yanagi-kimuralab/opensource-platform/OpenSource-Platform for publication/Parts/Driving crawler_Tensioner_Positioning plate _Inside.SLDPRT

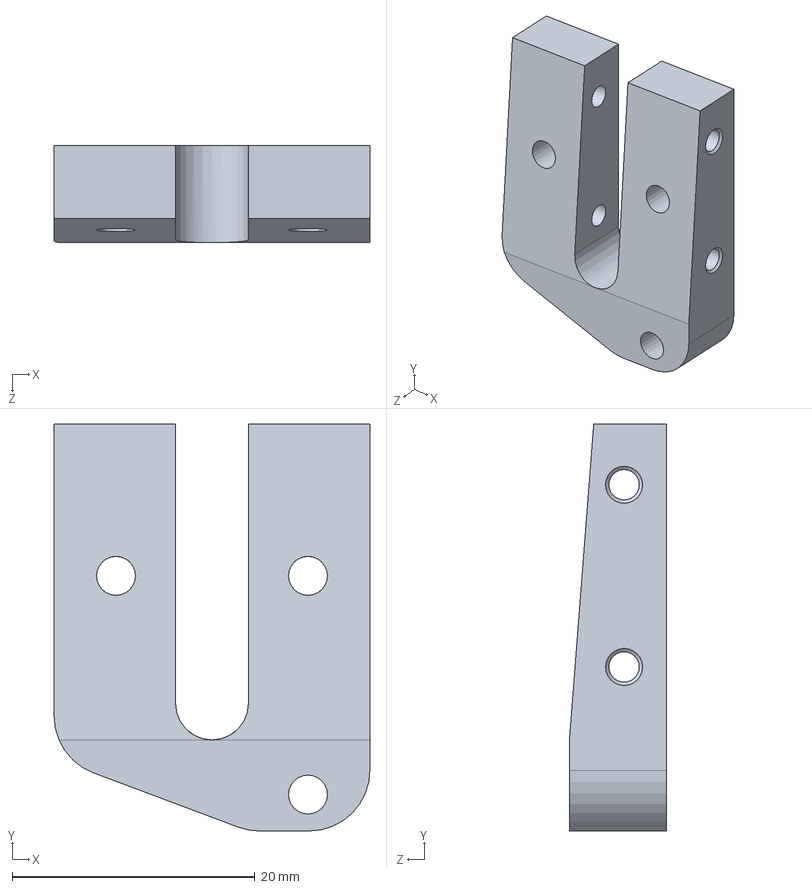
[picture p15: CAD file, 2023-01-07, last stored version]
OpenSource-Platform for publication/Parts/Driving crawler_Tensioner_Positioning plate _Inside.SLDPRT
26.0 x 33.5 x 8.00 mm
