yanagi-kimuralab/opensource-platform/OpenSource-Platform for publication/Ready-madeParts/PIJJ14-8-87.SLDPRT

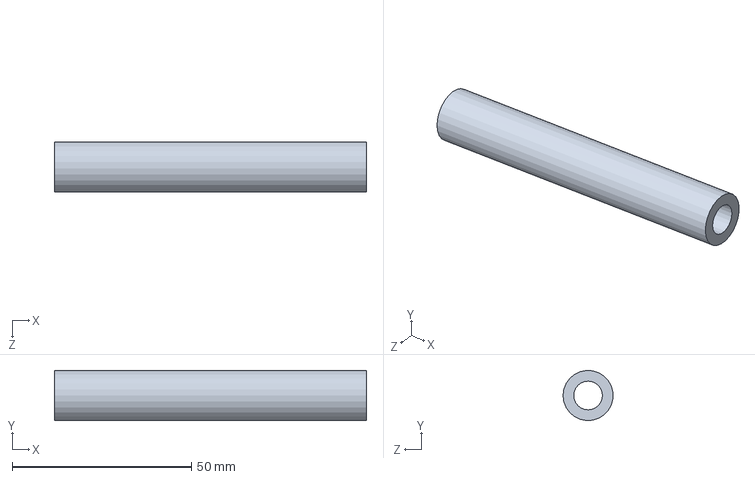
[picture p16: CAD file, 2023-01-07, last stored version]
OpenSource-Platform for publication/Ready-madeParts/PIJJ14-8-87.SLDPRT
87.0 x 14.0 x 13.9 mm
