yanagi-kimuralab/opensource-platform/OpenSource-Platform for publication/Ready-madeParts/内臓/NUC11PAHi7.SLDPRT

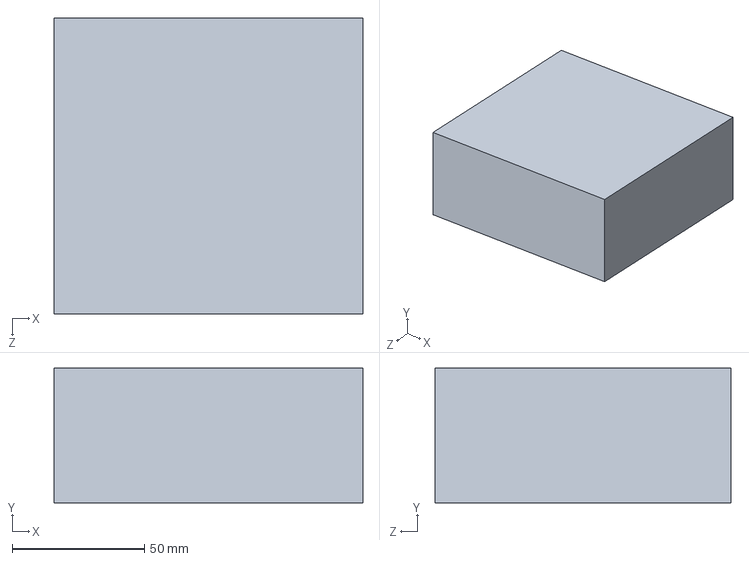
[picture p17: CAD file, 2023-01-07, last stored version]
OpenSource-Platform for publication/Ready-madeParts/内臓/NUC11PAHi7.SLDPRT
117.0 x 51.0 x 112.0 mm
