yanagi-kimuralab/opensource-platform/OpenSource-Platform for publication/jig/Flipper belt making jig.SLDPRT

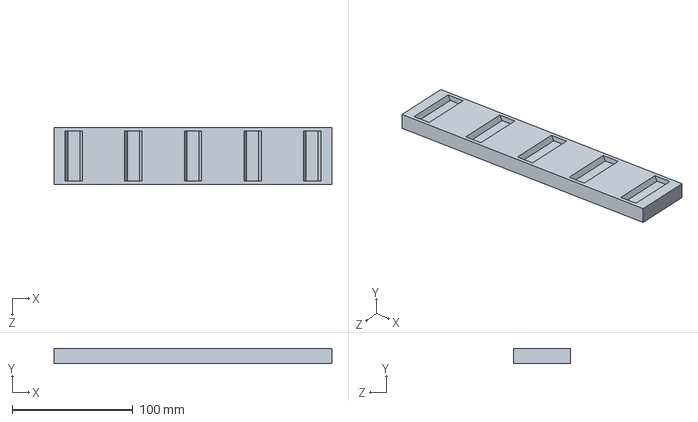
[picture p18: CAD file, 2023-01-07, last stored version]
OpenSource-Platform for publication/jig/Flipper belt making jig.SLDPRT
230.0 x 12.0 x 47.5 mm
