yanagi-kimuralab/opensource-platform/OpenSource-Platform for publication/Parts/Driving crawler_Tensioner_Shaft attachment.SLDPRT

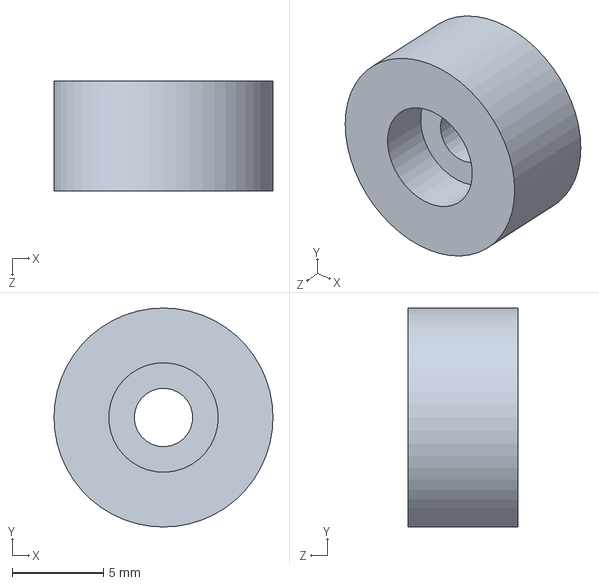
[picture p19: CAD file, 2023-01-07, last stored version]
OpenSource-Platform for publication/Parts/Driving crawler_Tensioner_Shaft attachment.SLDPRT
12.0 x 12.0 x 6.00 mm
