yanagi-kimuralab/opensource-platform/OpenSource-Platform for publication/Ready-madeParts/SLP9000A.SLDPRT

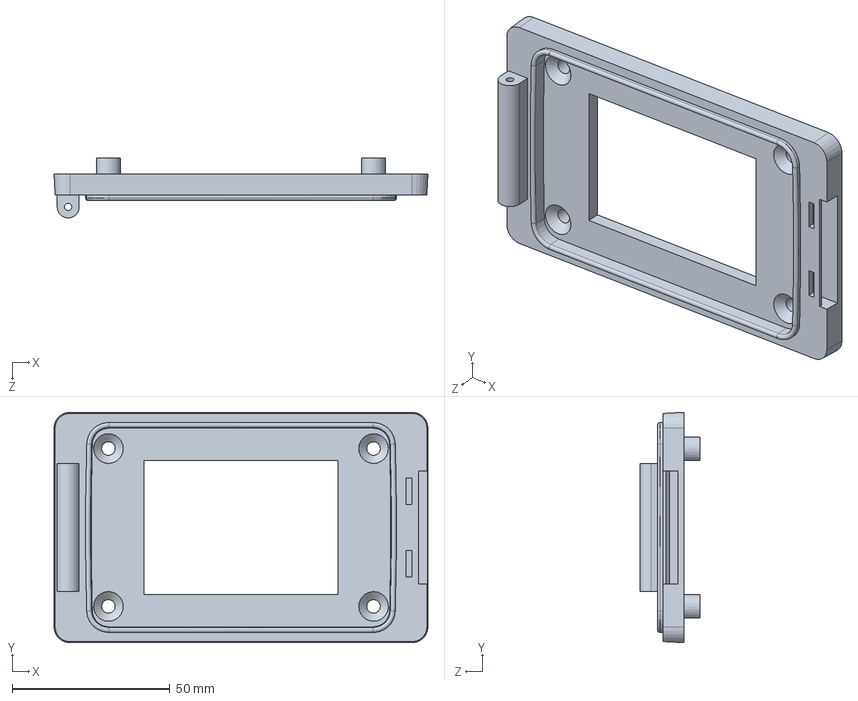
[picture p20: CAD file, 2023-01-07, last stored version]
OpenSource-Platform for publication/Ready-madeParts/SLP9000A.SLDPRT
118.5 x 73.0 x 19.0 mm
