yanagi-kimuralab/opensource-platform/OpenSource-Platform for publication/Ready-madeParts/内臓/ビデオサーバ.SLDPRT

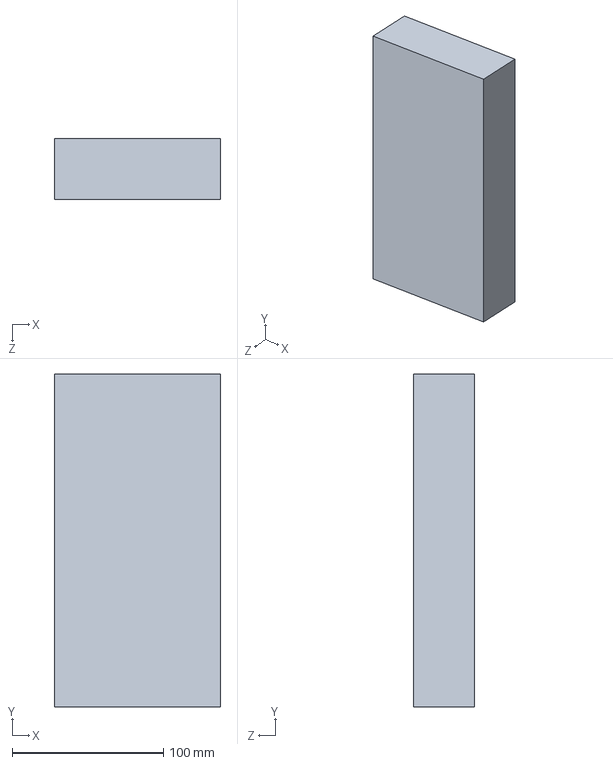
[picture p21: CAD file, 2023-01-07, last stored version]
OpenSource-Platform for publication/Ready-madeParts/内臓/ビデオサーバ.SLDPRT
110.0 x 220.0 x 40.0 mm
