yanagi-kimuralab/opensource-platform/OpenSource-Platform for publication/jig/Wart rubber cutting jig.SLDPRT

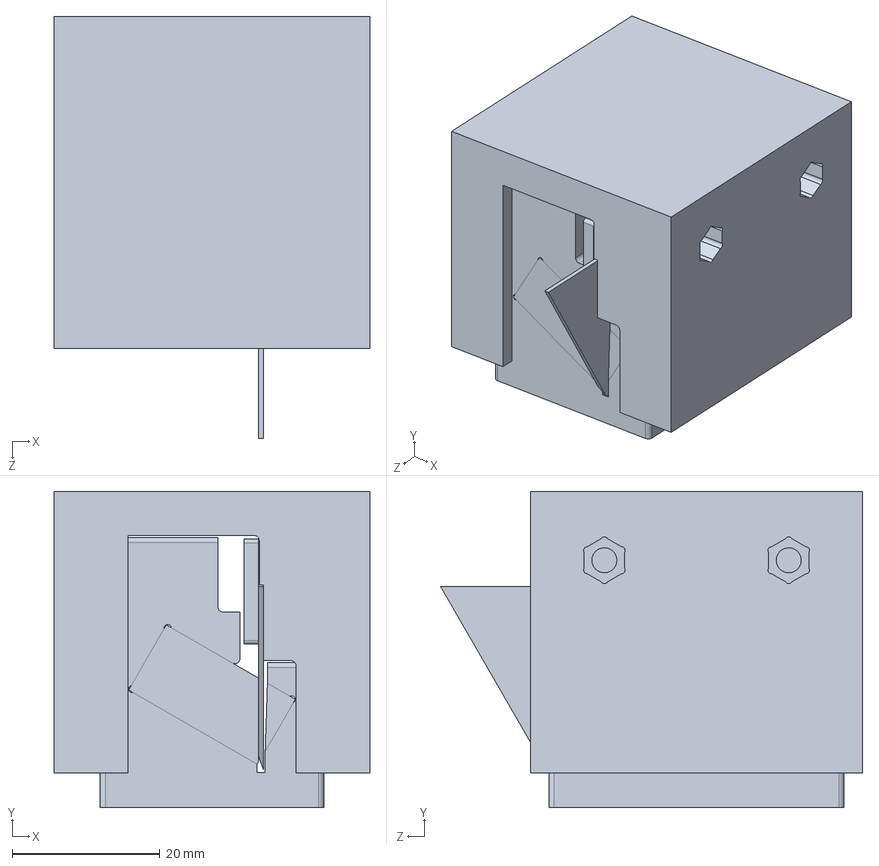
[picture p22: CAD file, 2023-01-07, last stored version]
OpenSource-Platform for publication/jig/Wart rubber cutting jig.SLDPRT
42.8 x 42.9 x 57.2 mm
