yanagi-kimuralab/opensource-platform/OpenSource-Platform for publication/Ready-madeParts/RDOS8-49.2-WMC4.SLDPRT

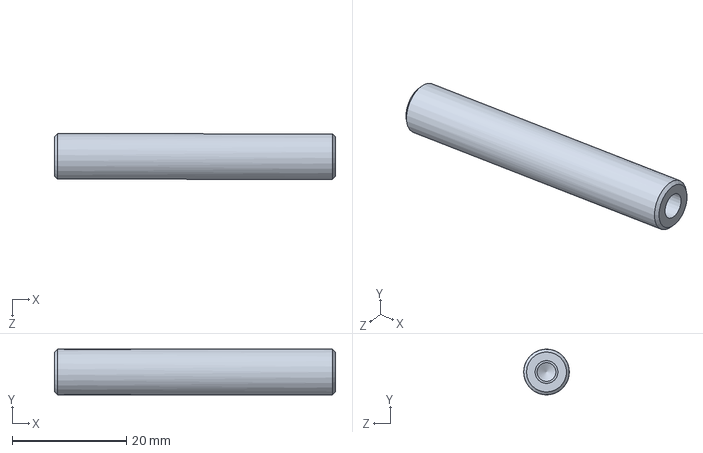
[picture p24: CAD file, 2023-01-07, last stored version]
OpenSource-Platform for publication/Ready-madeParts/RDOS8-49.2-WMC4.SLDPRT
49.2 x 7.98 x 8.00 mm
