yanagi-kimuralab/opensource-platform/OpenSource-Platform for publication/Ready-madeParts/内臓/バッテリー.SLDPRT

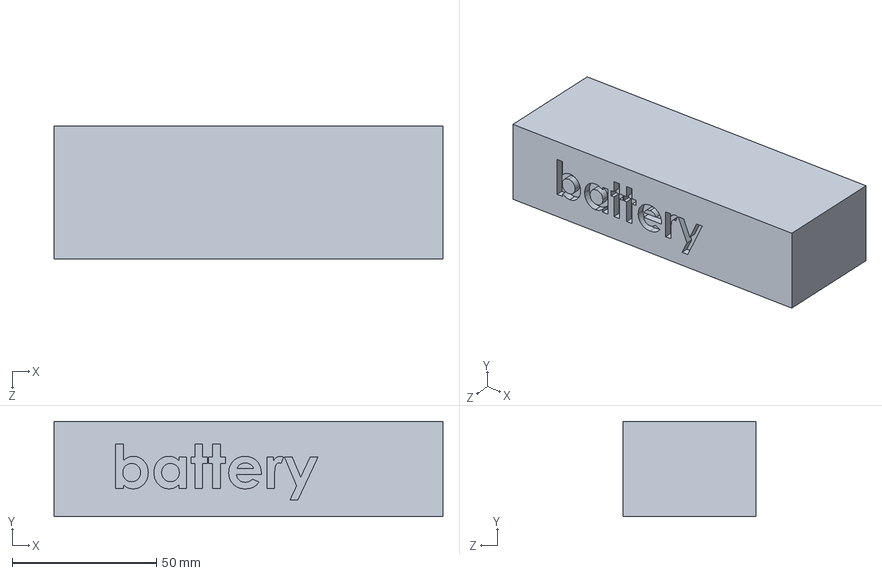
[picture p25: CAD file, 2023-01-07, last stored version]
OpenSource-Platform for publication/Ready-madeParts/内臓/バッテリー.SLDPRT
135.0 x 33.0 x 46.0 mm
