yanagi-kimuralab/opensource-platform/OpenSource-Platform for publication/Parts/Driving crawler_Tensioner_Positioning plate _Outside.SLDPRT

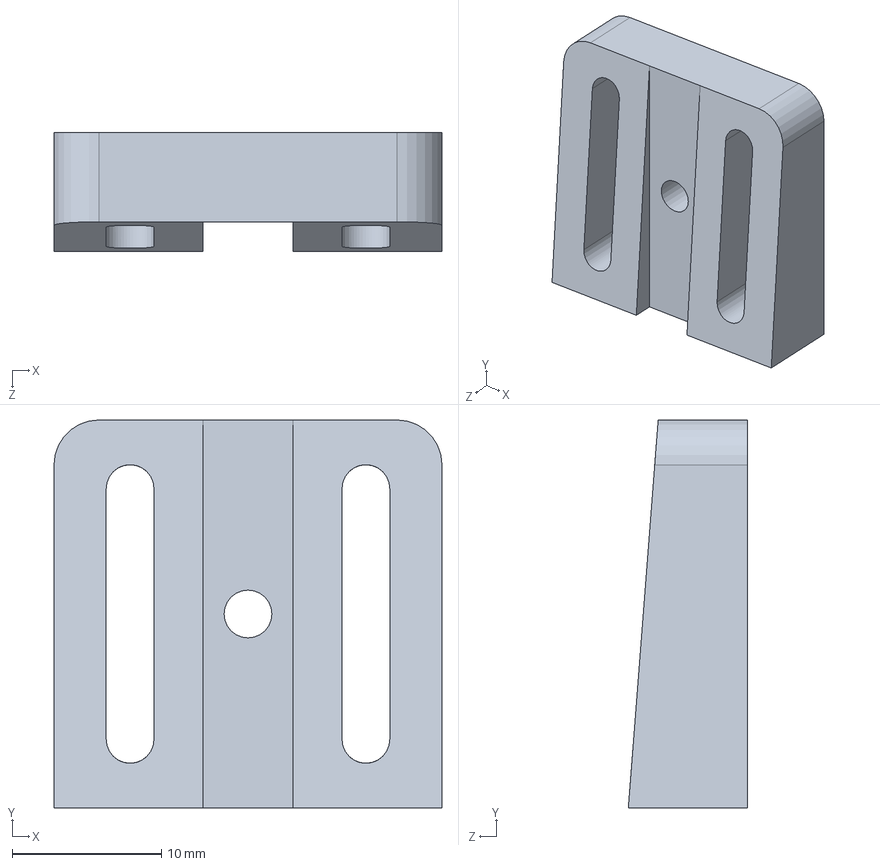
[picture p26: CAD file, 2023-01-07, last stored version]
OpenSource-Platform for publication/Parts/Driving crawler_Tensioner_Positioning plate _Outside.SLDPRT
26.0 x 26.0 x 8.00 mm
