yanagi-kimuralab/opensource-platform/OpenSource-Platform for publication/Ready-madeParts/SLP9000C.SLDPRT

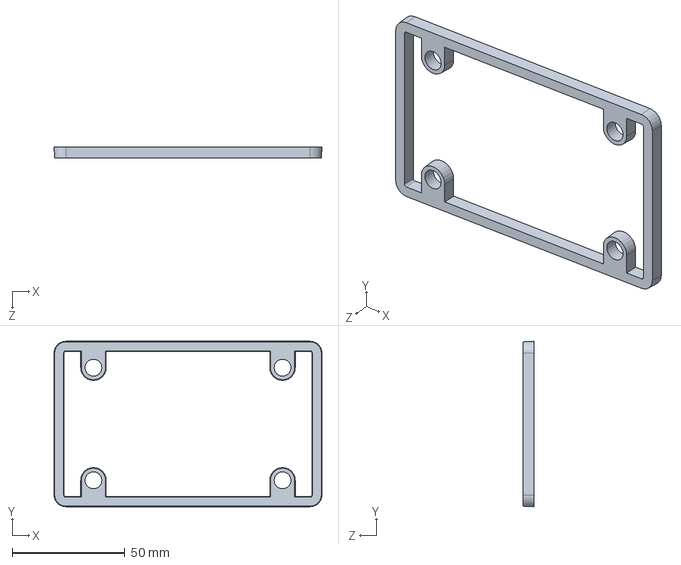
[picture p27: CAD file, 2023-01-07, last stored version]
OpenSource-Platform for publication/Ready-madeParts/SLP9000C.SLDPRT
119.0 x 73.5 x 5.00 mm
