yanagi-kimuralab/opensource-platform/OpenSource-Platform for publication/Parts/Driving crawler_Holding timing pulley plate_Base.SLDPRT

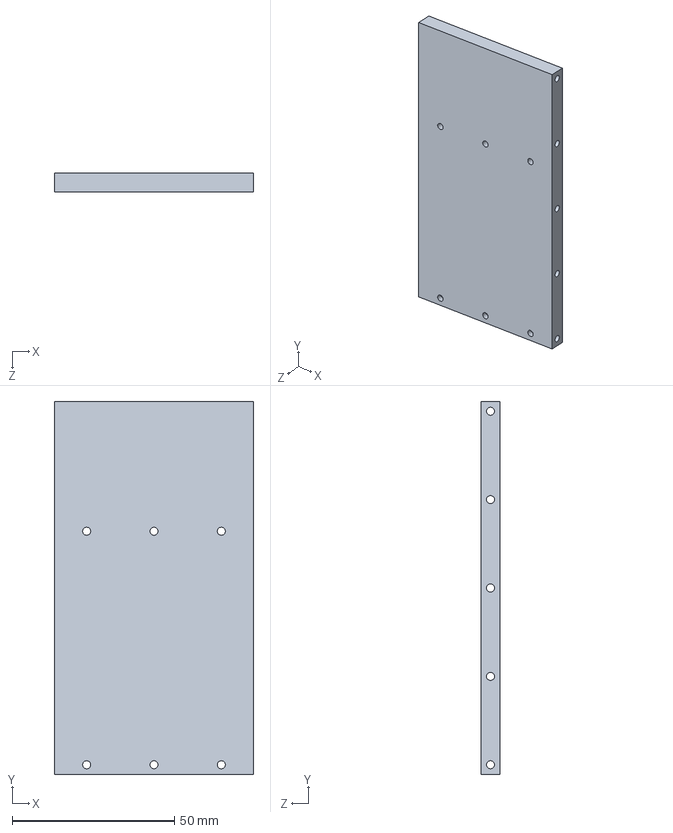
[picture p28: CAD file, 2023-01-07, last stored version]
OpenSource-Platform for publication/Parts/Driving crawler_Holding timing pulley plate_Base.SLDPRT
61.5 x 115.0 x 6.00 mm
