yanagi-kimuralab/opensource-platform/OpenSource-Platform for publication/Ready-madeParts/RDOS8-95-WMC4.SLDPRT

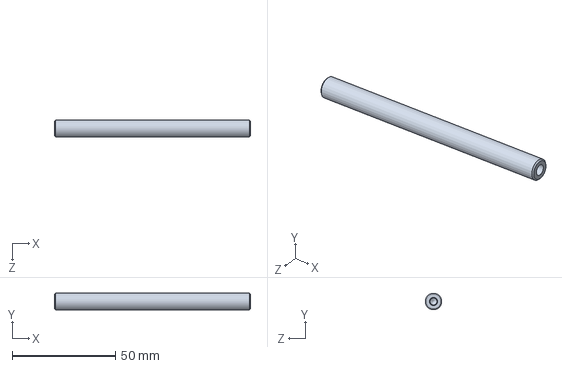
[picture p29: CAD file, 2023-01-07, last stored version]
OpenSource-Platform for publication/Ready-madeParts/RDOS8-95-WMC4.SLDPRT
95.0 x 8.00 x 8.00 mm
