yanagi-kimuralab/opensource-platform/OpenSource-Platform for publication/Ready-madeParts/内臓/OPENCR.SLDPRT

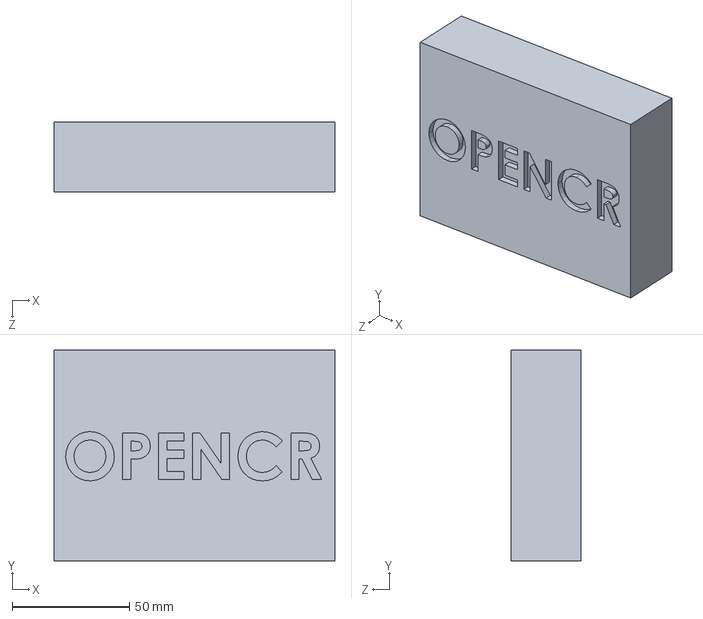
[picture p30: CAD file, 2023-01-07, last stored version]
OpenSource-Platform for publication/Ready-madeParts/内臓/OPENCR.SLDPRT
120.0 x 90.0 x 30.0 mm
