yanagi-kimuralab/opensource-platform/OpenSource-Platform for publication/Lid.sldprt

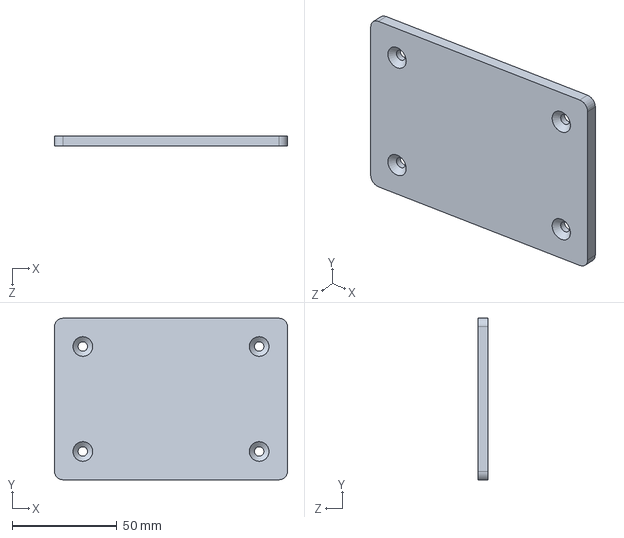
[picture p31: CAD file, 2023-01-07, last stored version]
OpenSource-Platform for publication/Lid.sldprt
111.0 x 77.0 x 5.00 mm
