yanagi-kimuralab/opensource-platform/OpenSource-Platform for publication/Parts/Driving crawler_Motor box_Plate_Side L R.SLDPRT

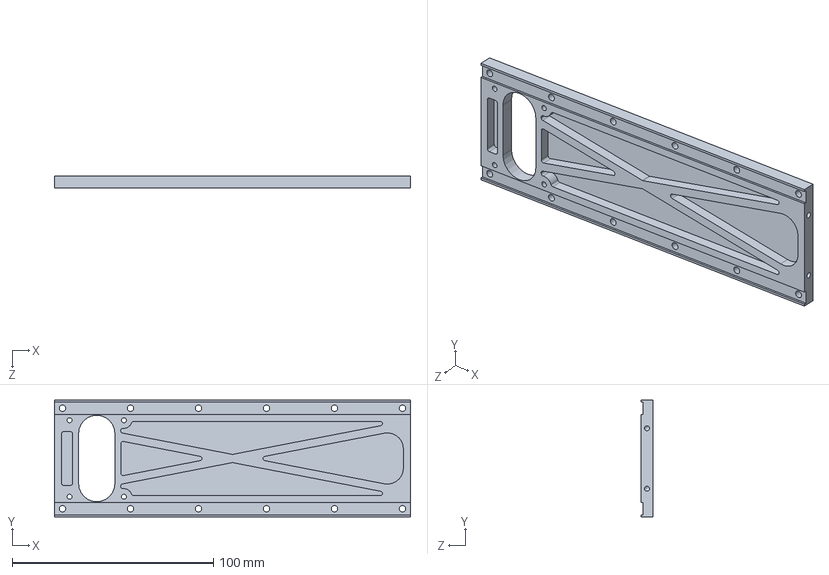
[picture p32: CAD file, 2023-01-07, last stored version]
OpenSource-Platform for publication/Parts/Driving crawler_Motor box_Plate_Side L R.SLDPRT
177.0 x 58.0 x 6.00 mm
