yanagi-kimuralab/opensource-platform/OpenSource-Platform for publication/Ready-madeParts/H54-200-S500-R.SLDPRT

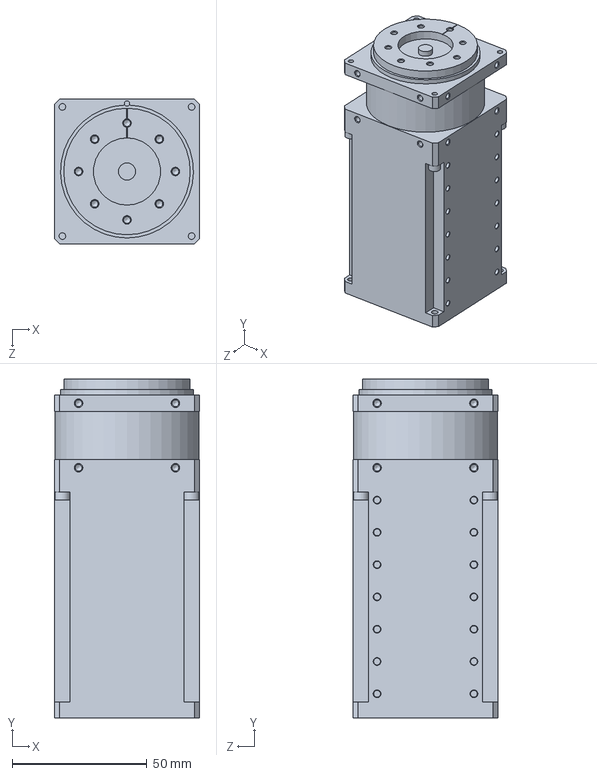
[picture p33: CAD file, 2023-01-07, last stored version]
OpenSource-Platform for publication/Ready-madeParts/H54-200-S500-R.SLDPRT
54.0 x 126.0 x 54.0 mm
