yanagi-kimuralab/opensource-platform/OpenSource-Platform for publication/Ready-madeParts/内臓/KYPOM K6 22.2V 3700mA 35C-70C.SLDPRT

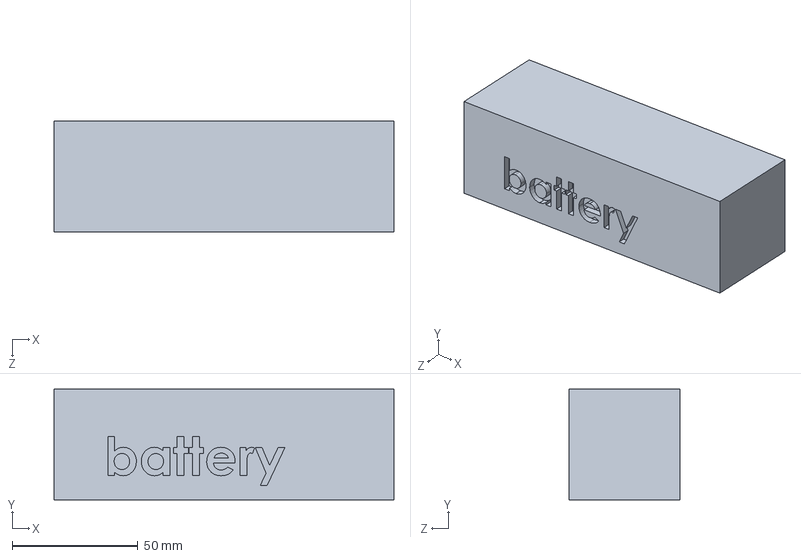
[picture p34: CAD file, 2023-01-07, last stored version]
OpenSource-Platform for publication/Ready-madeParts/内臓/KYPOM K6 22.2V 3700mA 35C-70C.SLDPRT
135.0 x 44.0 x 44.0 mm
