yanagi-kimuralab/opensource-platform/OpenSource-Platform for publication/Parts/Flipper_Connecting claw.SLDPRT

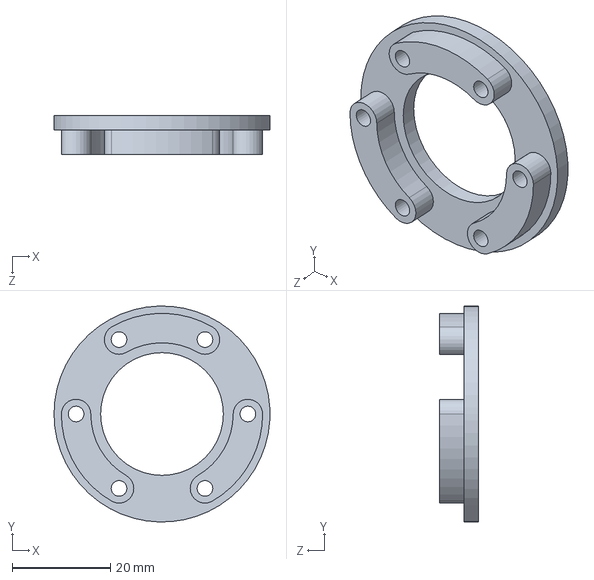
[picture p35: CAD file, 2023-01-07, last stored version]
OpenSource-Platform for publication/Parts/Flipper_Connecting claw.SLDPRT
44.0 x 44.0 x 8.00 mm
