yanagi-kimuralab/opensource-platform/OpenSource-Platform for publication/Ready-madeParts/FL6805ZZ.SLDPRT

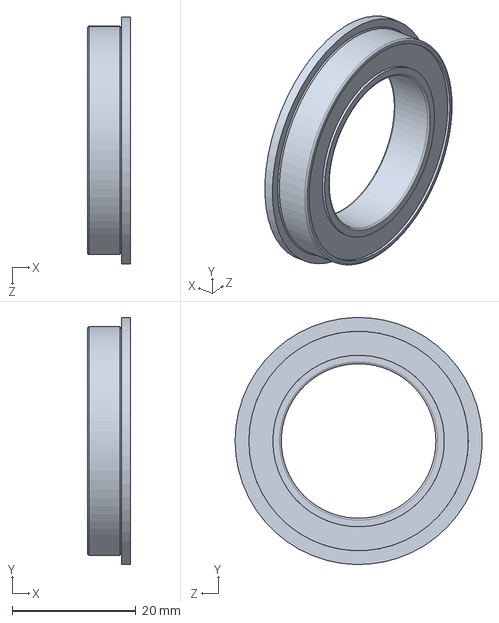
[picture p36: CAD file, 2023-01-07, last stored version]
OpenSource-Platform for publication/Ready-madeParts/FL6805ZZ.SLDPRT
7.00 x 40.0 x 40.0 mm
