yanagi-kimuralab/opensource-platform/OpenSource-Platform for publication/Ready-madeParts/内臓/48to24.SLDPRT

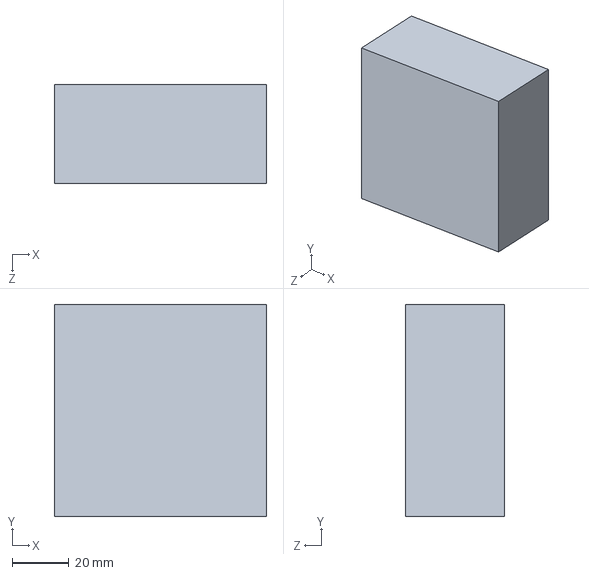
[picture p37: CAD file, 2023-01-07, last stored version]
OpenSource-Platform for publication/Ready-madeParts/内臓/48to24.SLDPRT
75.0 x 75.0 x 35.0 mm
