yanagi-kimuralab/opensource-platform/OpenSource-Platform for publication/Parts/Flipper_Timing pulley_Partition plate.SLDPRT

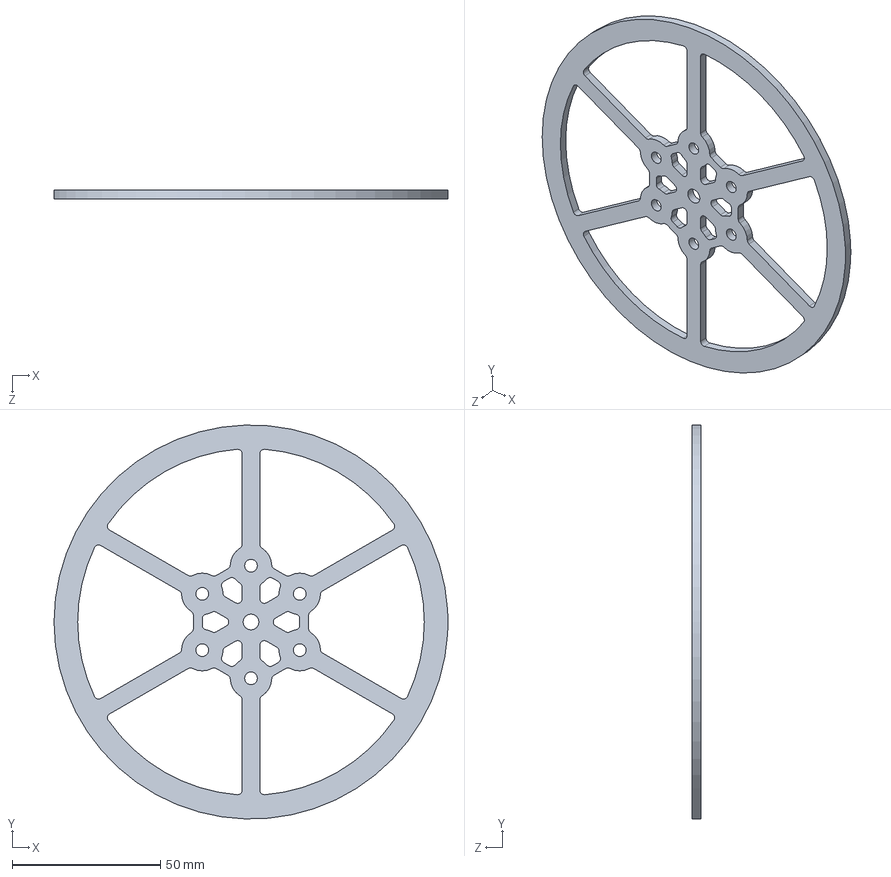
[picture p38: CAD file, 2023-01-07, last stored version]
OpenSource-Platform for publication/Parts/Flipper_Timing pulley_Partition plate.SLDPRT
133.0 x 132.9 x 3.00 mm
