yanagi-kimuralab/opensource-platform/OpenSource-Platform for publication/Ready-madeParts/KESF5-LC23.SLDPRT

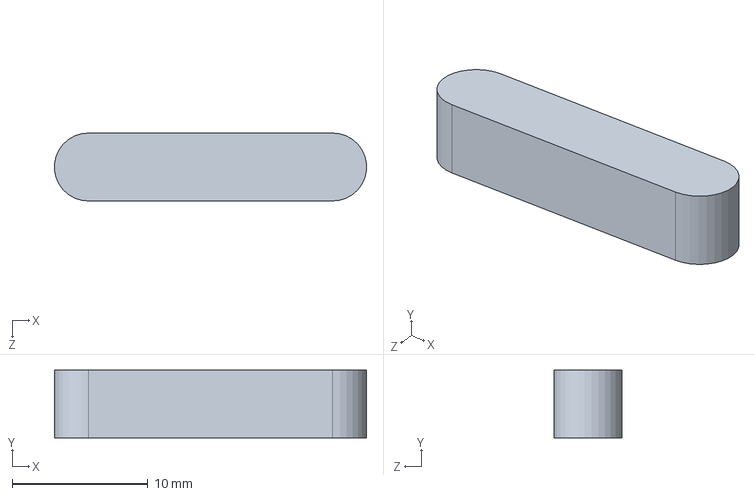
[picture p39: CAD file, 2023-01-07, last stored version]
OpenSource-Platform for publication/Ready-madeParts/KESF5-LC23.SLDPRT
23.0 x 5.00 x 5.00 mm
