yanagi-kimuralab/opensource-platform/OpenSource-Platform for publication/Ready-madeParts/内臓/NUC.SLDPRT

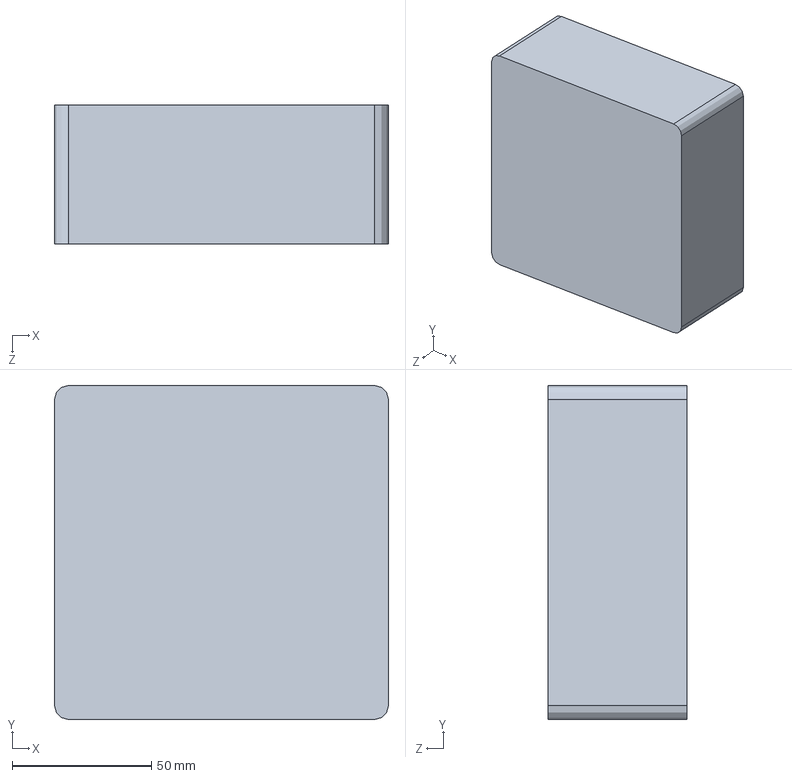
[picture p40: CAD file, 2023-01-07, last stored version]
OpenSource-Platform for publication/Ready-madeParts/内臓/NUC.SLDPRT
120.0 x 120.0 x 50.0 mm
