yanagi-kimuralab/opensource-platform/OpenSource-Platform for publication/Parts/Flipper_Timing pulley_Center attachment.SLDPRT

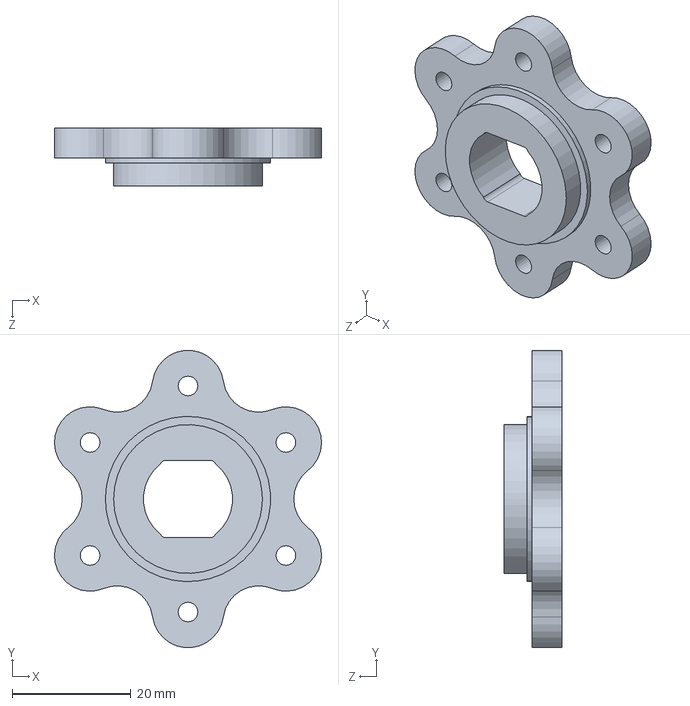
[picture p41: CAD file, 2023-01-07, last stored version]
OpenSource-Platform for publication/Parts/Flipper_Timing pulley_Center attachment.SLDPRT
44.9 x 49.9 x 9.70 mm
