yanagi-kimuralab/opensource-platform/OpenSource-Platform for publication/Ready-madeParts/B6800ZZ.SLDPRT

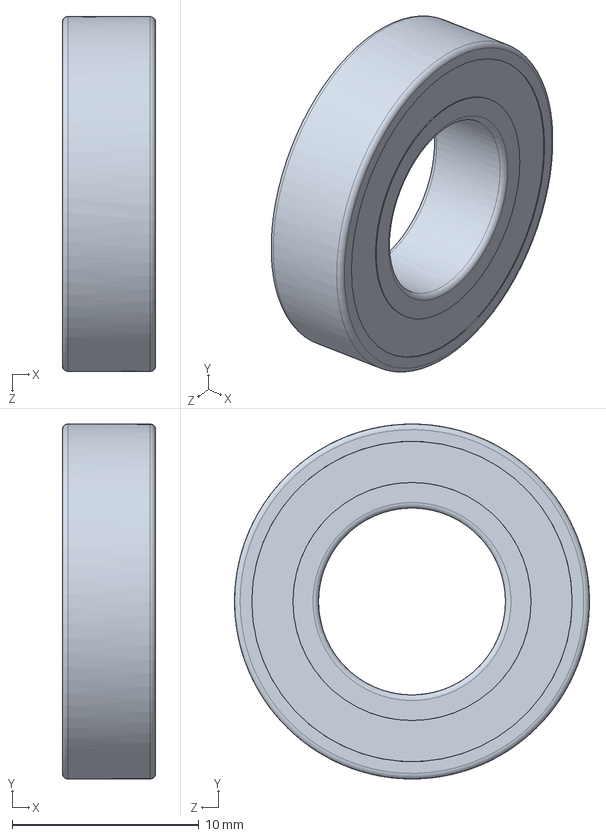
[picture p42: CAD file, 2023-01-07, last stored version]
OpenSource-Platform for publication/Ready-madeParts/B6800ZZ.SLDPRT
5.00 x 19.0 x 19.0 mm
