yanagi-kimuralab/opensource-platform/OpenSource-Platform for publication/Ready-madeParts/内臓/ｄｃｄｃ.SLDPRT

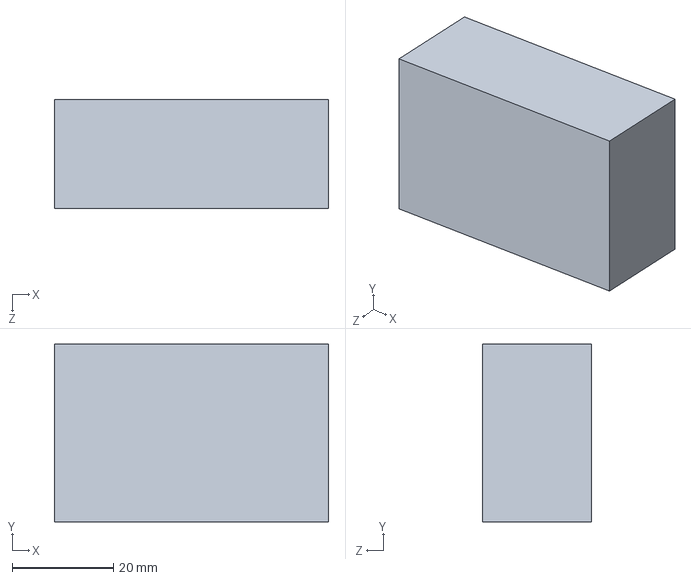
[picture p43: CAD file, 2023-01-07, last stored version]
OpenSource-Platform for publication/Ready-madeParts/内臓/ｄｃｄｃ.SLDPRT
54.0 x 35.0 x 21.5 mm
