yanagi-kimuralab/opensource-platform/OpenSource-Platform for publication/Parts/Flipper_Height adjustment plate for connecting claw.SLDPRT

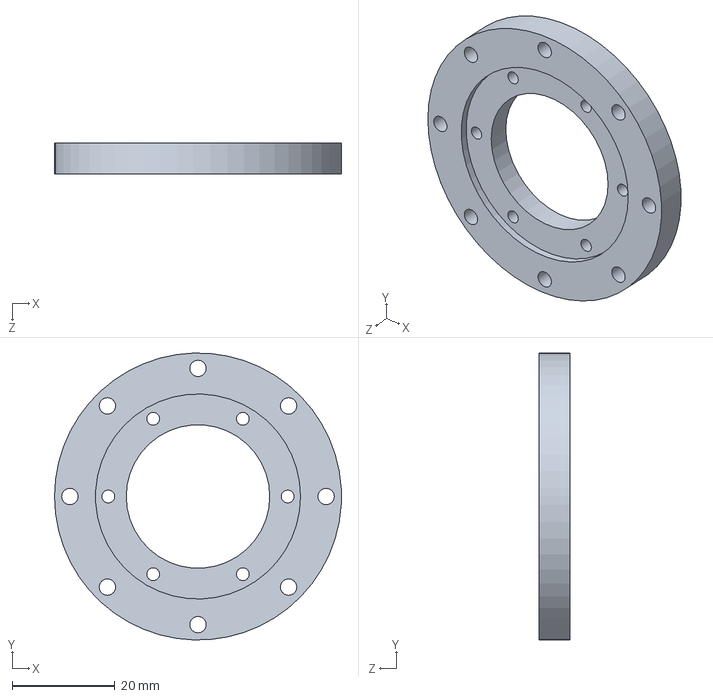
[picture p44: CAD file, 2023-01-07, last stored version]
OpenSource-Platform for publication/Parts/Flipper_Height adjustment plate for connecting claw.SLDPRT
56.0 x 56.0 x 6.00 mm
