yanagi-kimuralab/opensource-platform/OpenSource-Platform for publication/Ready-madeParts/内臓/ビデオサーバー.SLDPRT

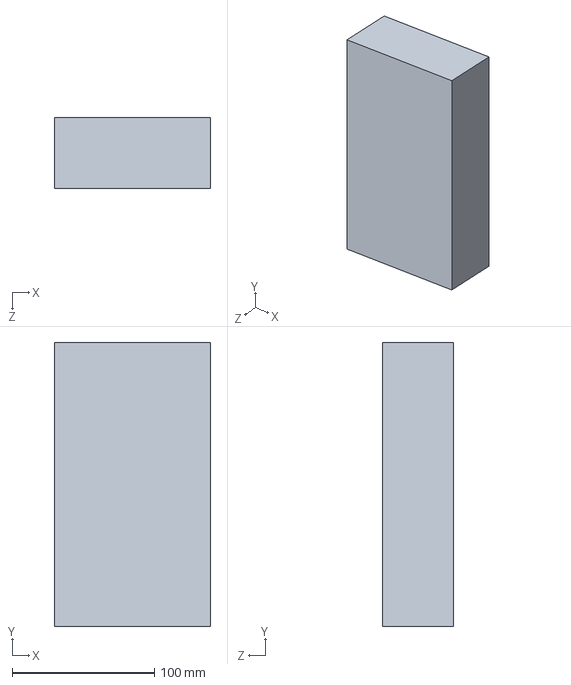
[picture p45: CAD file, 2023-01-07, last stored version]
OpenSource-Platform for publication/Ready-madeParts/内臓/ビデオサーバー.SLDPRT
110.0 x 200.0 x 50.0 mm
