yanagi-kimuralab/opensource-platform/OpenSource-Platform for publication/Parts/Driving flipper_Motor box_Outside cap.SLDPRT

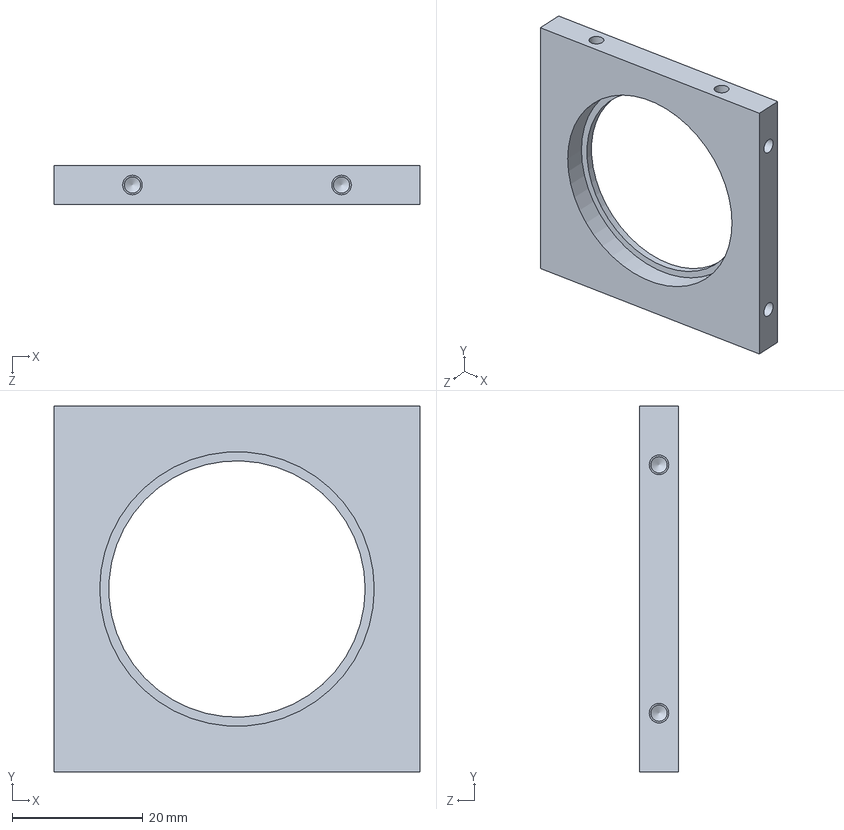
[picture p46: CAD file, 2023-01-07, last stored version]
OpenSource-Platform for publication/Parts/Driving flipper_Motor box_Outside cap.SLDPRT
56.0 x 56.0 x 6.00 mm
