yanagi-kimuralab/opensource-platform/OpenSource-Platform for publication/Ready-madeParts/HPB-4X25-SUS.SLDPRT

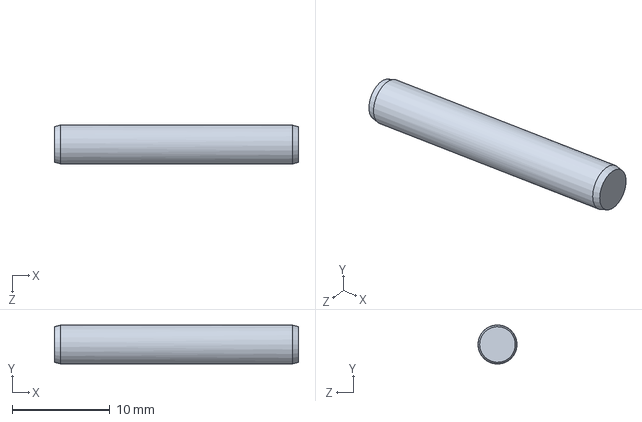
[picture p47: CAD file, 2023-01-07, last stored version]
OpenSource-Platform for publication/Ready-madeParts/HPB-4X25-SUS.SLDPRT
25.0 x 3.99 x 4.00 mm
