yanagi-kimuralab/opensource-platform/OpenSource-Platform for publication/Ready-madeParts/内臓/端子台.SLDPRT

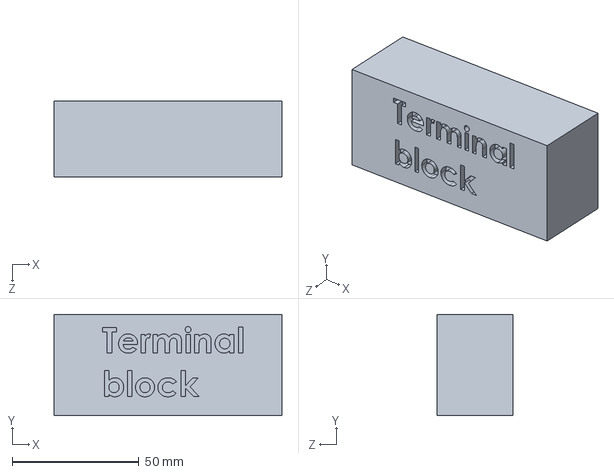
[picture p48: CAD file, 2023-01-07, last stored version]
OpenSource-Platform for publication/Ready-madeParts/内臓/端子台.SLDPRT
90.0 x 40.0 x 30.0 mm
