yanagi-kimuralab/opensource-platform/OpenSource-Platform for publication/Parts/Flipper_Idler_Center attachment.SLDPRT

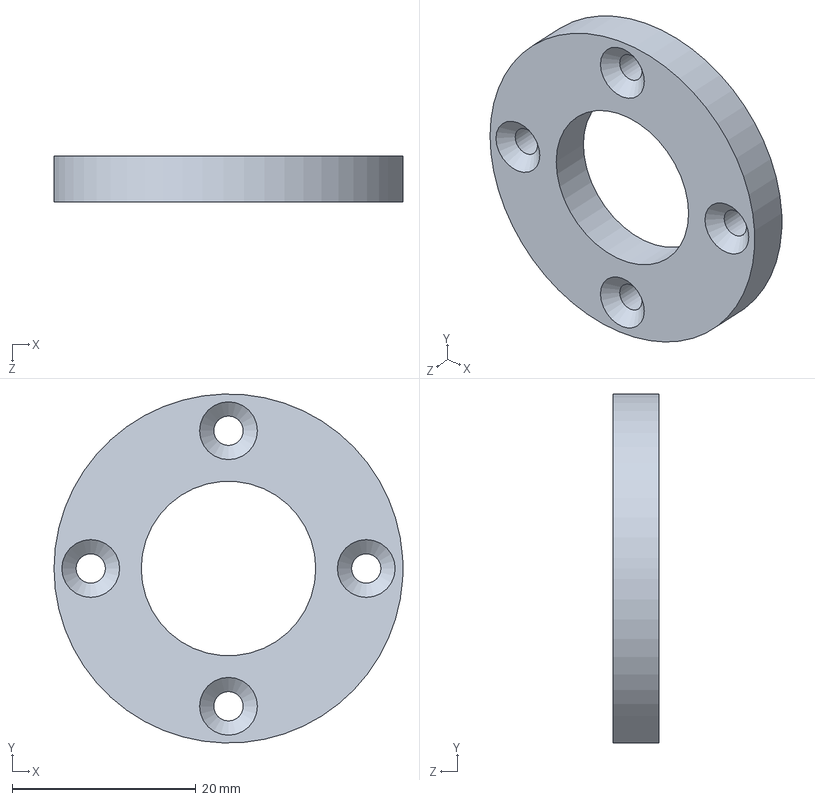
[picture p49: CAD file, 2023-01-07, last stored version]
OpenSource-Platform for publication/Parts/Flipper_Idler_Center attachment.SLDPRT
38.0 x 38.0 x 5.00 mm
