yanagi-kimuralab/opensource-platform/OpenSource-Platform for publication/Ready-madeParts/RDOS8-65.5-WMC4.SLDPRT

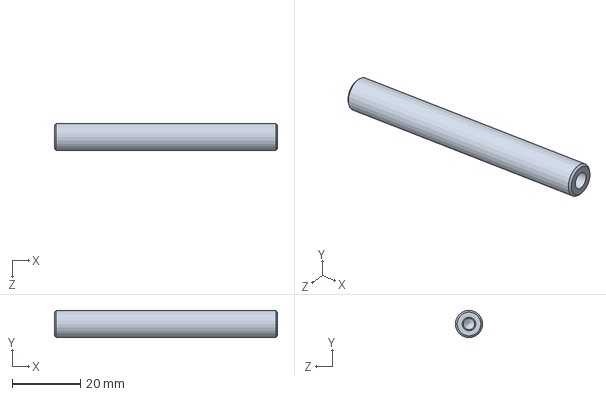
[picture p50: CAD file, 2023-01-07, last stored version]
OpenSource-Platform for publication/Ready-madeParts/RDOS8-65.5-WMC4.SLDPRT
65.5 x 8.00 x 8.00 mm
