yanagi-kimuralab/opensource-platform/OpenSource-Platform for publication/Ready-madeParts/内臓/EPOS.SLDPRT

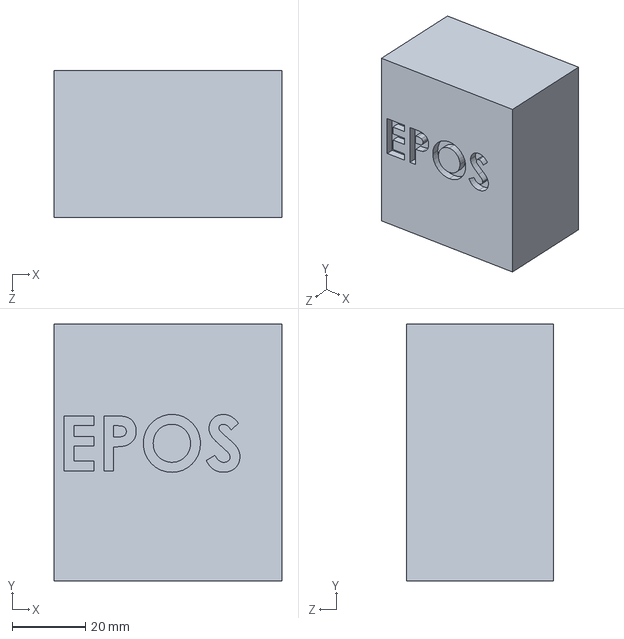
[picture p51: CAD file, 2023-01-07, last stored version]
OpenSource-Platform for publication/Ready-madeParts/内臓/EPOS.SLDPRT
62.0 x 70.0 x 40.0 mm
