yanagi-kimuralab/opensource-platform/OpenSource-Platform for publication/Parts/Driving crawler_Tensioner_Holding cantilever.SLDPRT

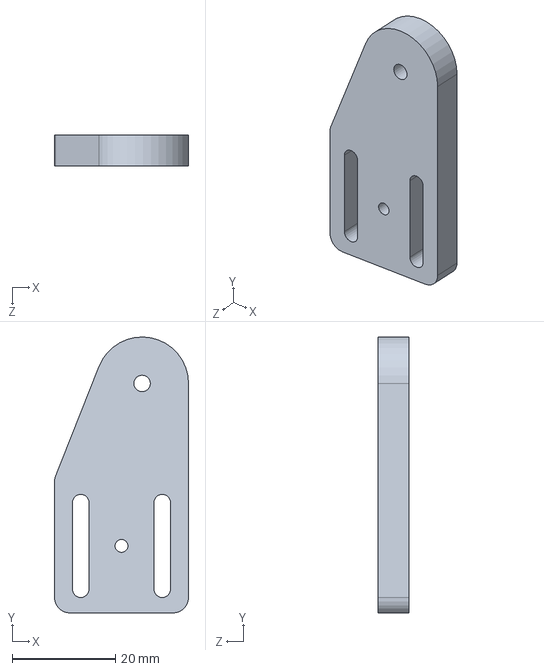
[picture p52: CAD file, 2023-01-07, last stored version]
OpenSource-Platform for publication/Parts/Driving crawler_Tensioner_Holding cantilever.SLDPRT
26.0 x 53.5 x 6.00 mm
