yanagi-kimuralab/opensource-platform/OpenSource-Platform for publication/Ready-madeParts/NGS25.SLDPRT

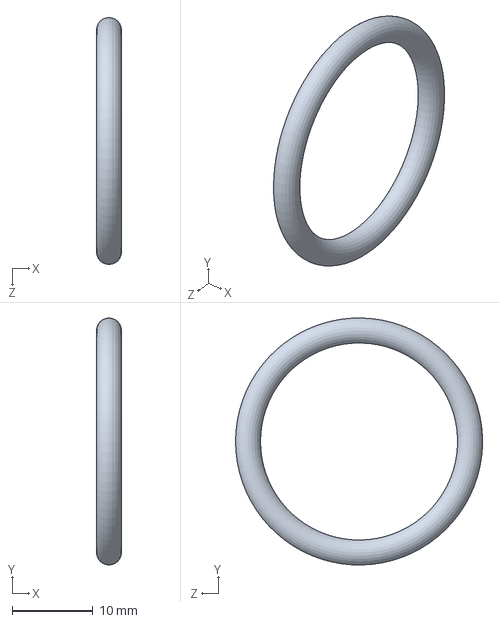
[picture p53: CAD file, 2023-01-07, last stored version]
OpenSource-Platform for publication/Ready-madeParts/NGS25.SLDPRT
3.10 x 30.6 x 30.6 mm
