yanagi-kimuralab/opensource-platform/OpenSource-Platform for publication/Ready-madeParts/内臓/B08ZCV1Q2T.SLDPRT

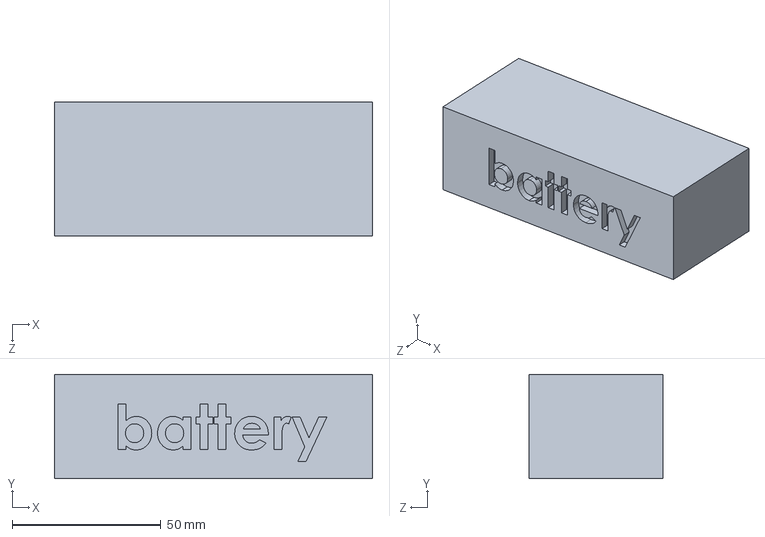
[picture p54: CAD file, 2023-01-07, last stored version]
OpenSource-Platform for publication/Ready-madeParts/内臓/B08ZCV1Q2T.SLDPRT
107.0 x 35.0 x 45.0 mm
