yanagi-kimuralab/opensource-platform/OpenSource-Platform for publication/Parts/Driving crawler_Bearing holder.SLDPRT

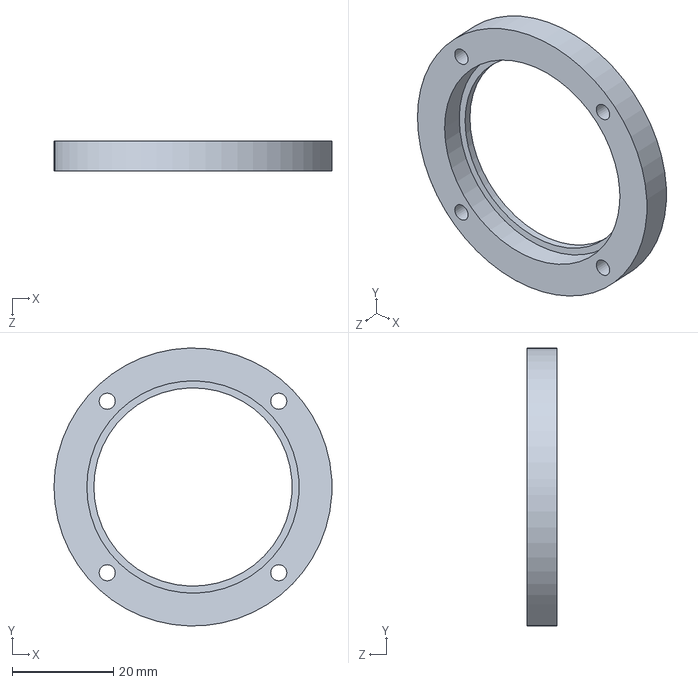
[picture p55: CAD file, 2023-01-07, last stored version]
OpenSource-Platform for publication/Parts/Driving crawler_Bearing holder.SLDPRT
55.0 x 55.0 x 6.00 mm
