yanagi-kimuralab/opensource-platform/OpenSource-Platform for publication/Ready-madeParts/ロボトップ(DPC3-SB_2517)AWG14(2.0sq)2c.SLDPRT

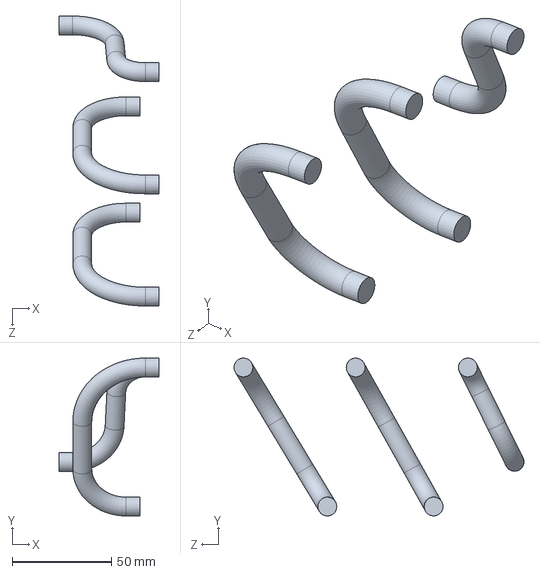
[picture p56: CAD file, 2023-01-07, last stored version]
OpenSource-Platform for publication/Ready-madeParts/ロボトップ(DPC3-SB_2517)AWG14(2.0sq)2c.SLDPRT
50.5 x 79.5 x 146.0 mm
