yanagi-kimuralab/opensource-platform/OpenSource-Platform for publication/Ready-madeParts/内臓/Arduino.SLDPRT

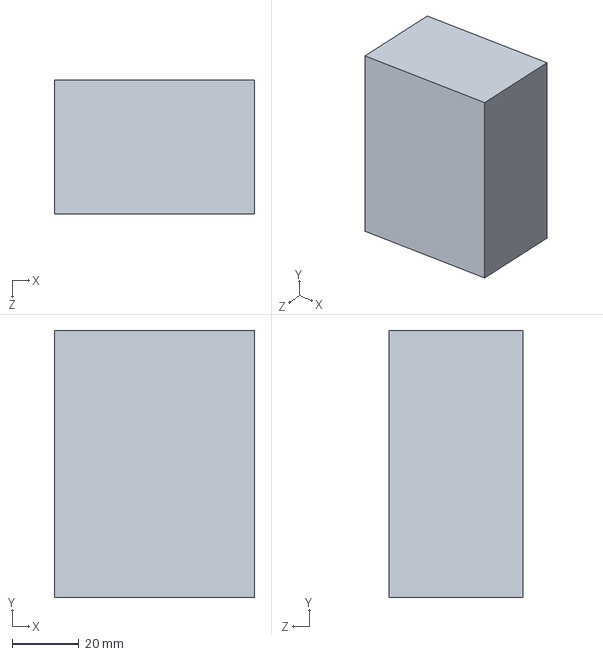
[picture p57: CAD file, 2023-01-07, last stored version]
OpenSource-Platform for publication/Ready-madeParts/内臓/Arduino.SLDPRT
60.0 x 80.0 x 40.0 mm
