yanagi-kimuralab/opensource-platform/OpenSource-Platform for publication/Parts/Driving crawler_Motor box_Plate_Side A B.SLDPRT

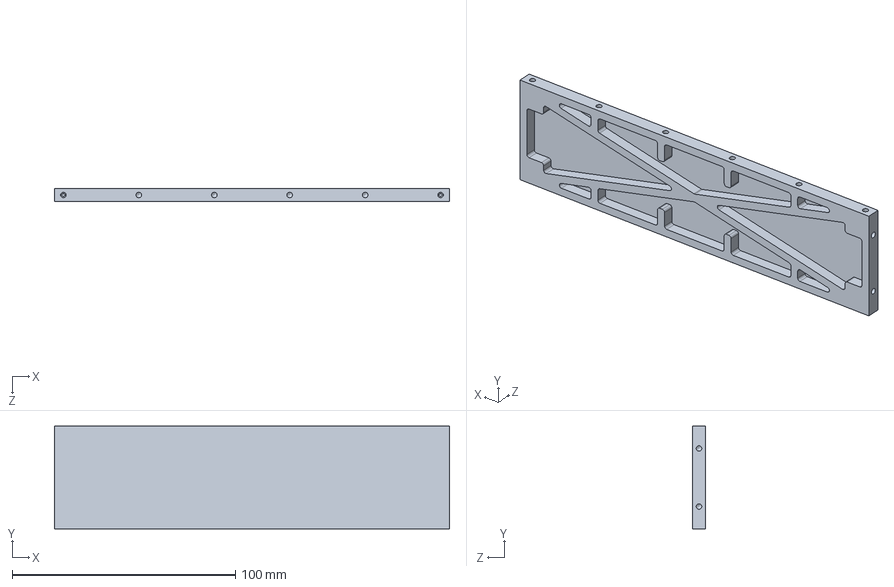
[picture p58: CAD file, 2023-01-07, last stored version]
OpenSource-Platform for publication/Parts/Driving crawler_Motor box_Plate_Side A B.SLDPRT
177.0 x 46.0 x 6.00 mm
