yanagi-kimuralab/opensource-platform/OpenSource-Platform for publication/Ready-madeParts/T-145825.SLDPRT

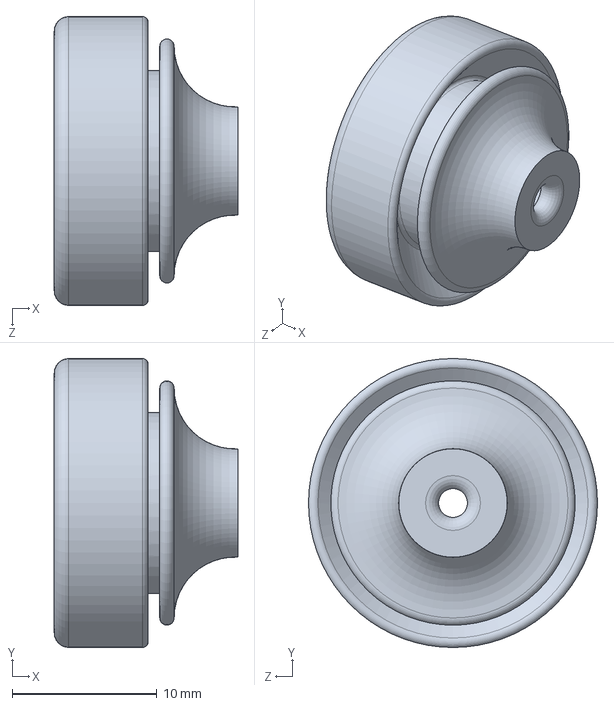
[picture p59: CAD file, 2023-01-07, last stored version]
OpenSource-Platform for publication/Ready-madeParts/T-145825.SLDPRT
12.7 x 20.0 x 20.0 mm
