yanagi-kimuralab/opensource-platform/OpenSource-Platform for publication/Parts/Driving crawler_Timing pulley shaft_Spacer.SLDPRT

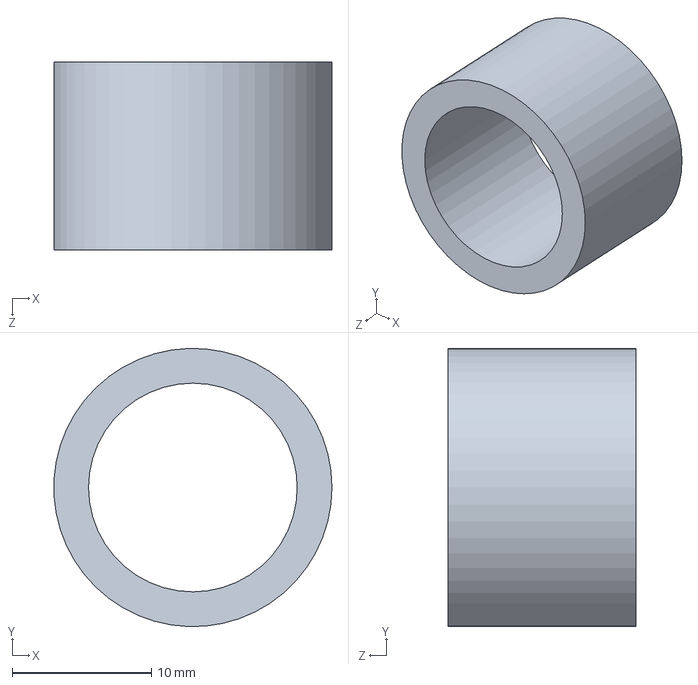
[picture p60: CAD file, 2023-01-07, last stored version]
OpenSource-Platform for publication/Parts/Driving crawler_Timing pulley shaft_Spacer.SLDPRT
20.0 x 20.0 x 13.5 mm
