yanagi-kimuralab/opensource-platform/OpenSource-Platform for publication/Ready-madeParts/JZF6-10.SLDPRT

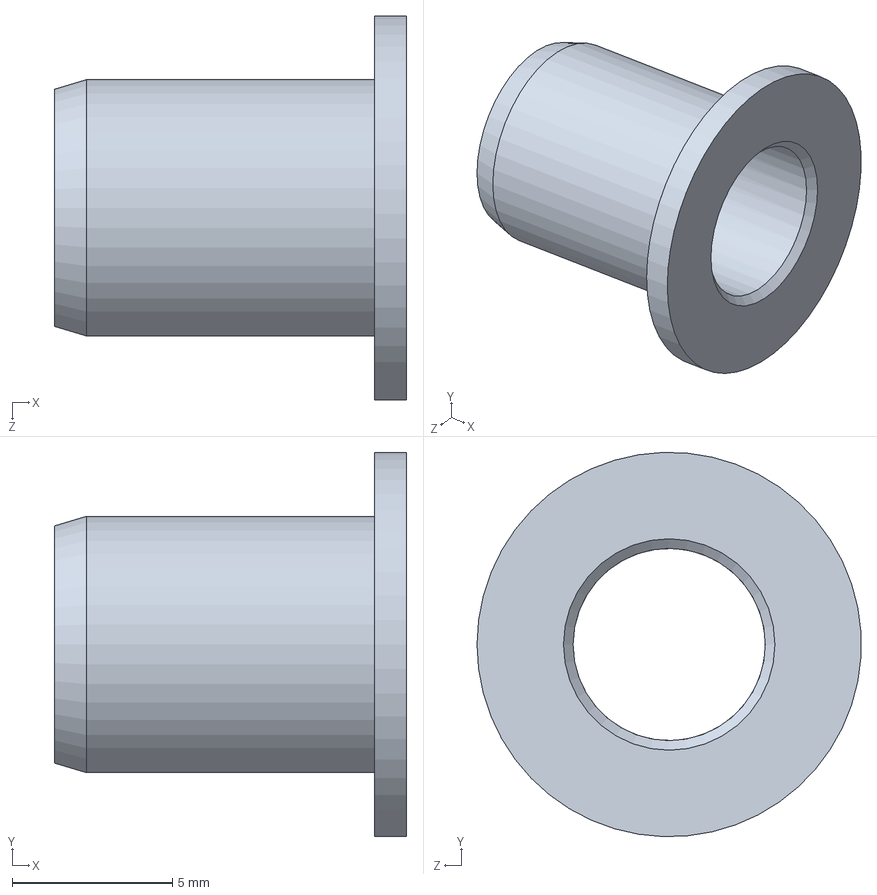
[picture p61: CAD file, 2023-01-07, last stored version]
OpenSource-Platform for publication/Ready-madeParts/JZF6-10.SLDPRT
11.0 x 12.0 x 12.0 mm
