yanagi-kimuralab/opensource-platform/OpenSource-Platform for publication/Ready-madeParts/KRT AWG28 X 10C 5m^OpenSource.sldprt

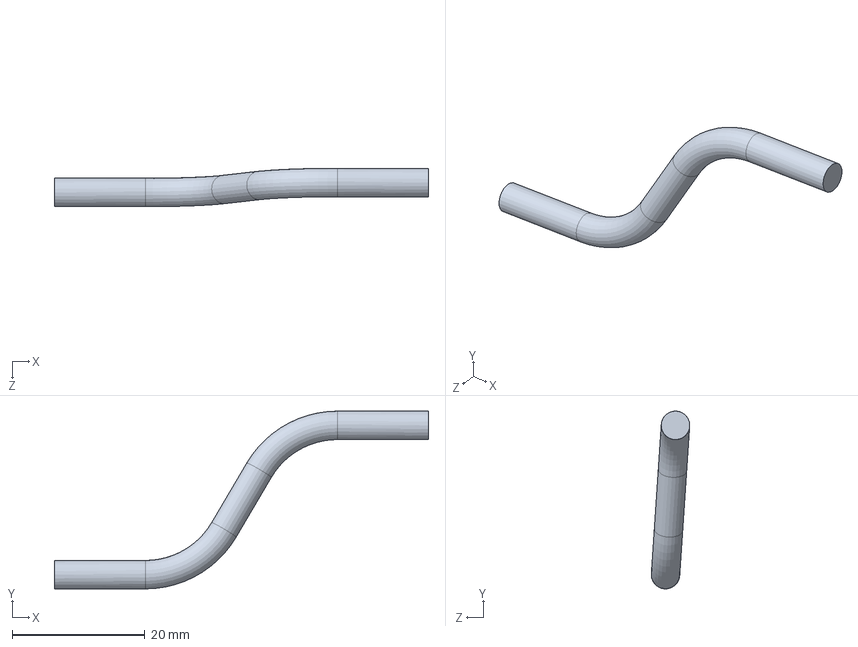
[picture p62: CAD file, 2023-01-07, last stored version]
OpenSource-Platform for publication/Ready-madeParts/KRT AWG28 X 10C 5m^OpenSource.sldprt
56.4 x 26.8 x 5.80 mm
