yanagi-kimuralab/opensource-platform/OpenSource-Platform for publication/Parts/Circuit box_Above loft plate.SLDPRT

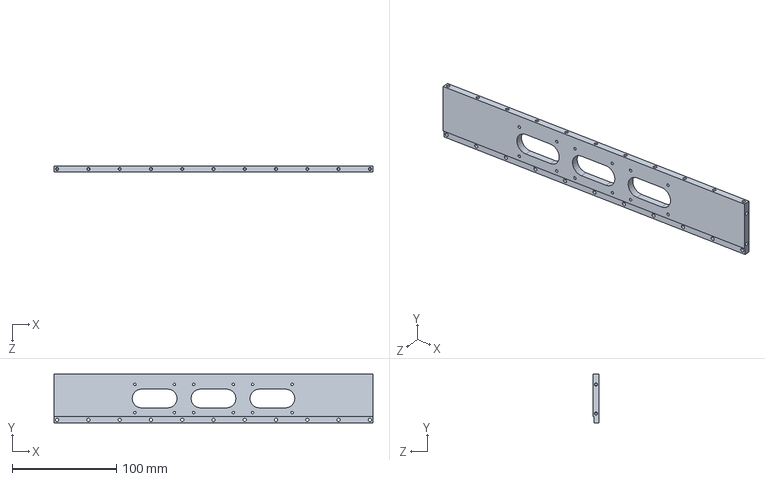
[picture p63: CAD file, 2023-01-07, last stored version]
OpenSource-Platform for publication/Parts/Circuit box_Above loft plate.SLDPRT
306.0 x 47.0 x 6.00 mm
