yanagi-kimuralab/opensource-platform/OpenSource-Platform for publication/Ready-madeParts/B07YHJK4LN.SLDPRT

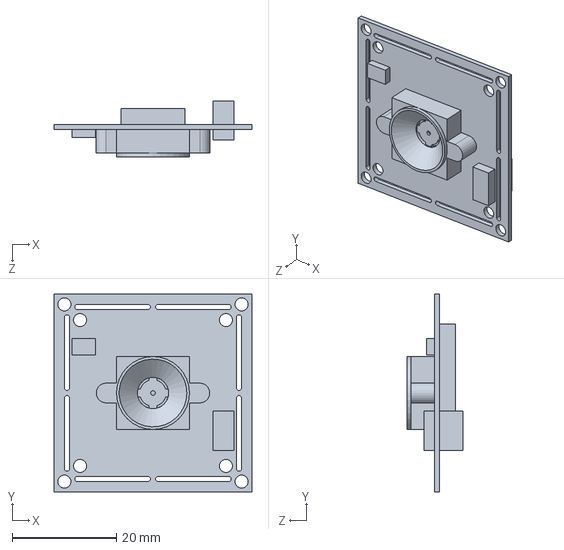
[picture p65: CAD file, 2023-01-07, last stored version]
OpenSource-Platform for publication/Ready-madeParts/B07YHJK4LN.SLDPRT
38.0 x 38.0 x 10.8 mm
