yanagi-kimuralab/opensource-platform/OpenSource-Platform for publication/Parts/Driving crawler_Driven pulley.SLDPRT

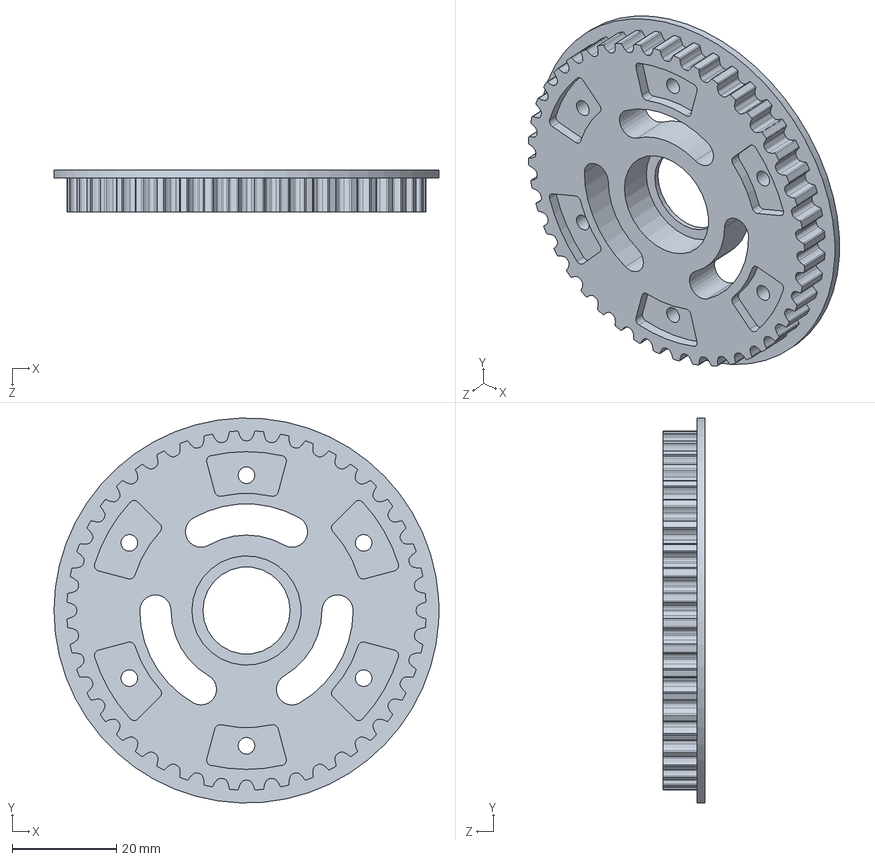
[picture p66: CAD file, 2023-01-07, last stored version]
OpenSource-Platform for publication/Parts/Driving crawler_Driven pulley.SLDPRT
74.0 x 74.0 x 8.00 mm
