yanagi-kimuralab/opensource-platform/OpenSource-Platform for publication/Ready-madeParts/KEGS5-LC30.SLDPRT

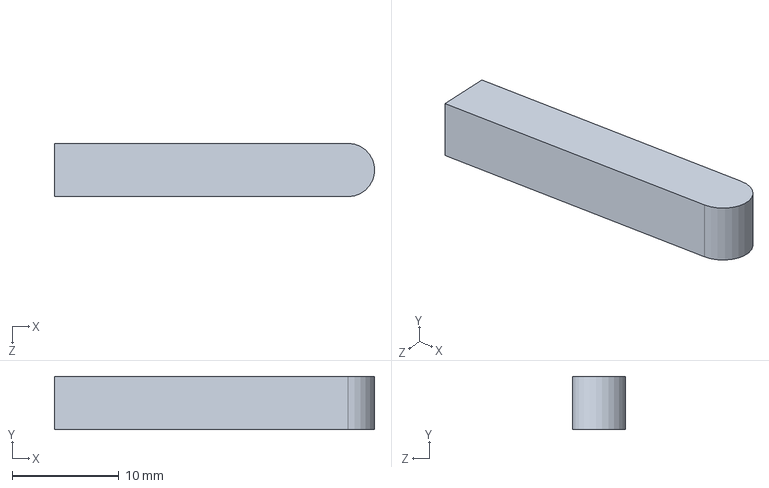
[picture p67: CAD file, 2023-01-07, last stored version]
OpenSource-Platform for publication/Ready-madeParts/KEGS5-LC30.SLDPRT
30.0 x 5.00 x 5.00 mm
