yanagi-kimuralab/opensource-platform/OpenSource-Platform for publication/Parts/Driving flipper_Drive pulley.SLDPRT

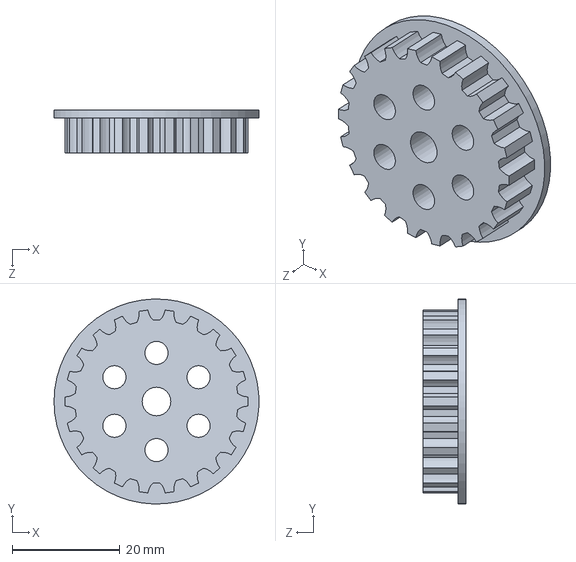
[picture p68: CAD file, 2023-01-07, last stored version]
OpenSource-Platform for publication/Parts/Driving flipper_Drive pulley.SLDPRT
38.0 x 38.0 x 8.00 mm
