yanagi-kimuralab/opensource-platform/OpenSource-Platform for publication/Ready-madeParts/SSFHRW15-75-MD5-ND5-KC45-A30-SFC0-SG16-AG180.SLDPRT

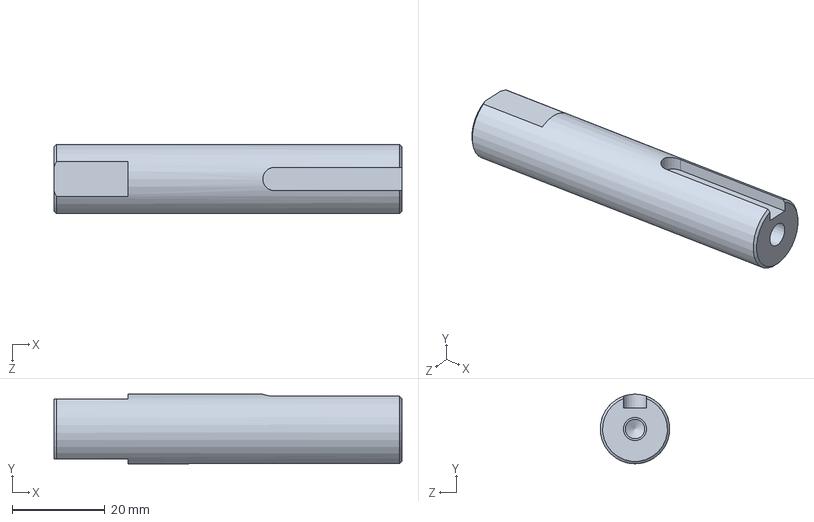
[picture p69: CAD file, 2023-01-07, last stored version]
OpenSource-Platform for publication/Ready-madeParts/SSFHRW15-75-MD5-ND5-KC45-A30-SFC0-SG16-AG180.SLDPRT
75.0 x 15.0 x 14.9 mm
