yanagi-kimuralab/opensource-platform/OpenSource-Platform for publication/Parts/Driving crawler_Holding timing pulley plate_Mirror.SLDPRT

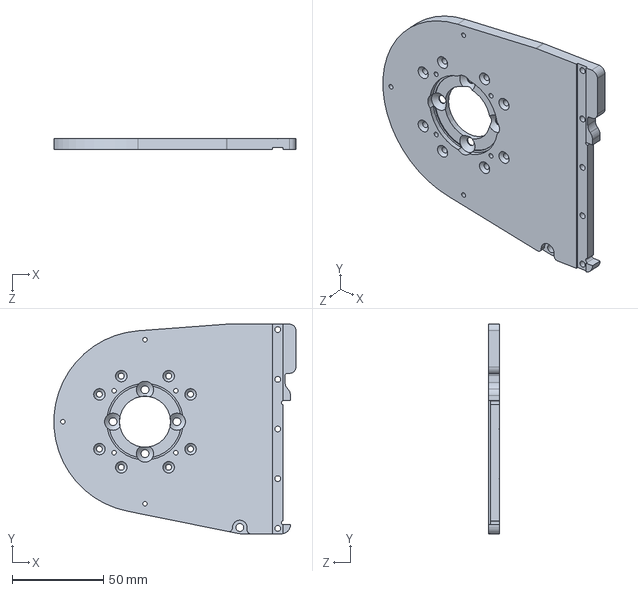
[picture p70: CAD file, 2023-01-07, last stored version]
OpenSource-Platform for publication/Parts/Driving crawler_Holding timing pulley plate_Mirror.SLDPRT
132.7 x 115.0 x 6.00 mm
