yanagi-kimuralab/opensource-platform/OpenSource-Platform for publication/Ready-madeParts/RDOS6-99-WMC3.SLDPRT

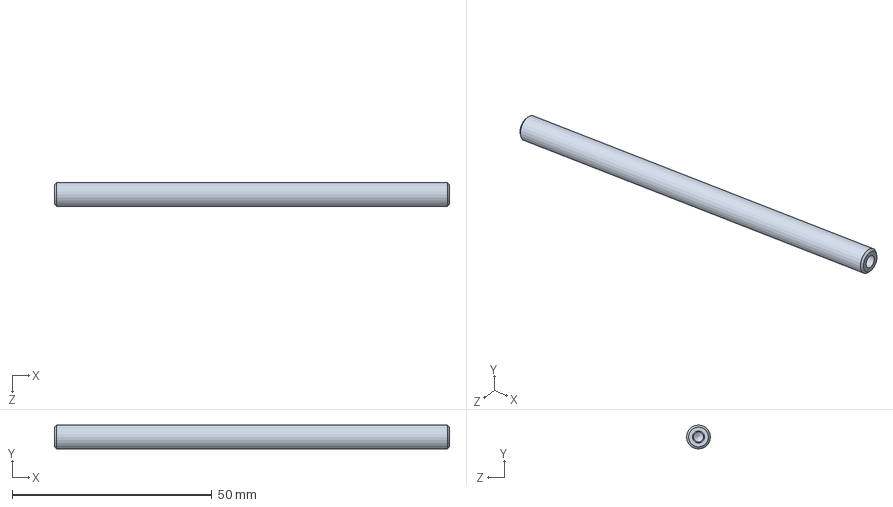
[picture p71: CAD file, 2023-01-07, last stored version]
OpenSource-Platform for publication/Ready-madeParts/RDOS6-99-WMC3.SLDPRT
99.0 x 6.00 x 6.00 mm
