yanagi-kimuralab/opensource-platform/OpenSource-Platform for publication/Parts/Driving flipper_Attachment for motor.SLDPRT

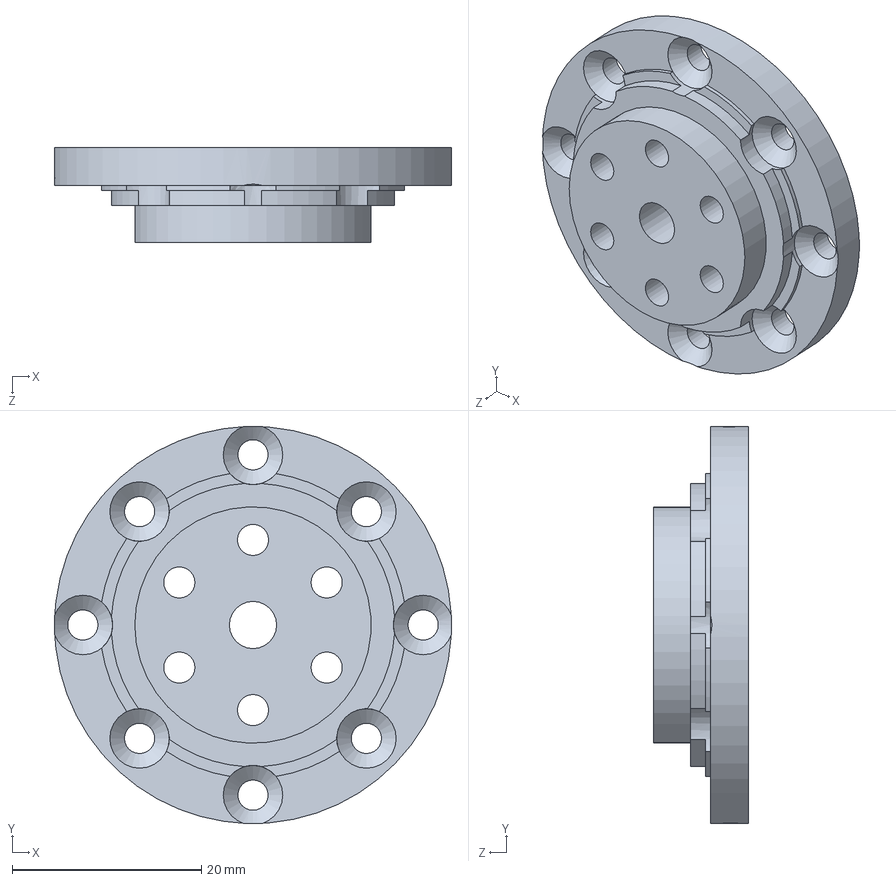
[picture p72: CAD file, 2023-01-07, last stored version]
OpenSource-Platform for publication/Parts/Driving flipper_Attachment for motor.SLDPRT
42.0 x 42.0 x 10.0 mm
