yanagi-kimuralab/opensource-platform/OpenSource-Platform for publication/Ready-madeParts/S36-1A.SLDPRT

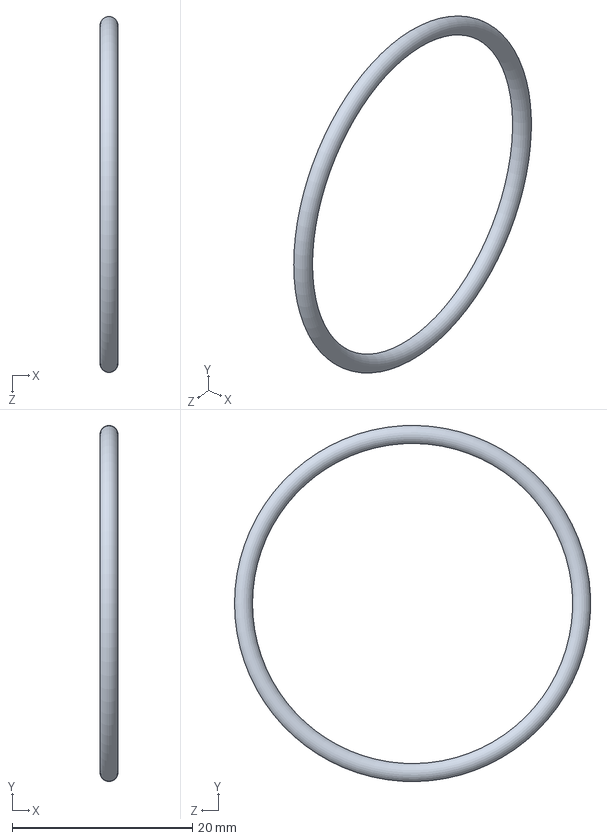
[picture p73: CAD file, 2023-01-07, last stored version]
OpenSource-Platform for publication/Ready-madeParts/S36-1A.SLDPRT
2.00 x 39.5 x 39.5 mm
