yanagi-kimuralab/opensource-platform/OpenSource-Platform for publication/Parts/Middle part^Camera mount.sldprt

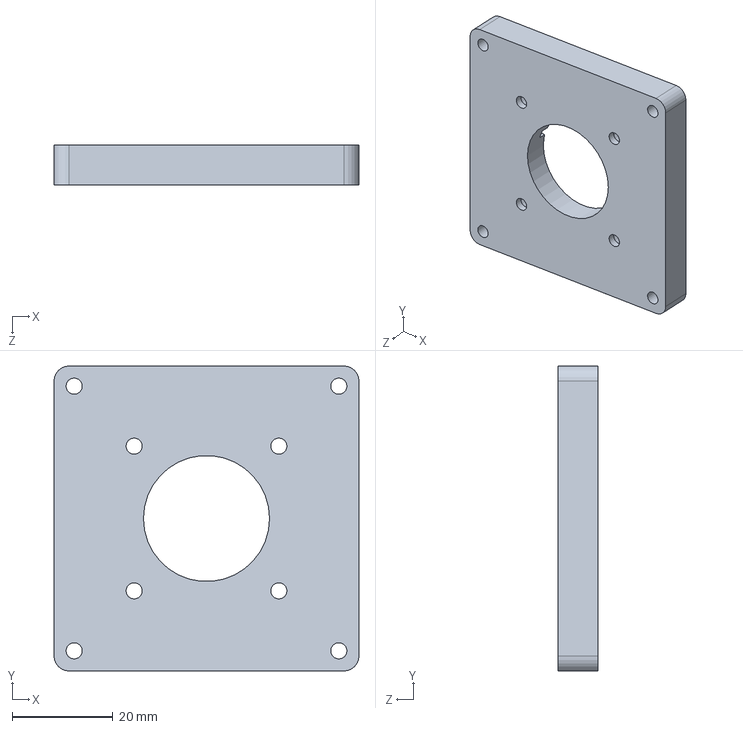
[picture p74: CAD file, 2023-01-07, last stored version]
OpenSource-Platform for publication/Parts/Middle part^Camera mount.sldprt
60.5 x 60.5 x 8.00 mm
