yanagi-kimuralab/opensource-platform/OpenSource-Platform for publication/Ready-madeParts/R-TW1530.SLDPRT

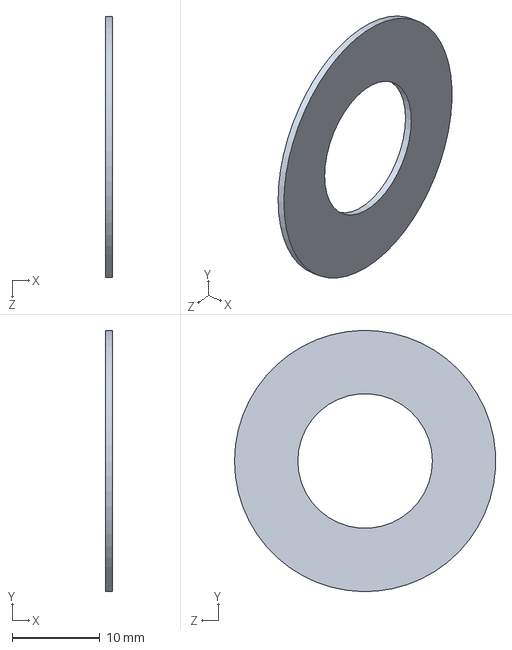
[picture p75: CAD file, 2023-01-07, last stored version]
OpenSource-Platform for publication/Ready-madeParts/R-TW1530.SLDPRT
0.8 x 29.7 x 29.7 mm
