yanagi-kimuralab/opensource-platform/OpenSource-Platform for publication/Parts/Front part^Camera mount.sldprt

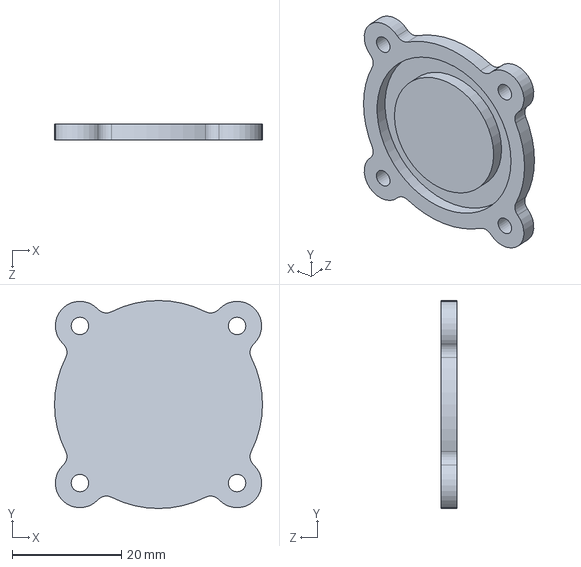
[picture p76: CAD file, 2023-01-07, last stored version]
OpenSource-Platform for publication/Parts/Front part^Camera mount.sldprt
38.0 x 38.0 x 3.00 mm
