yanagi-kimuralab/opensource-platform/OpenSource-Platform for publication/Ready-madeParts/HK1512.SLDPRT

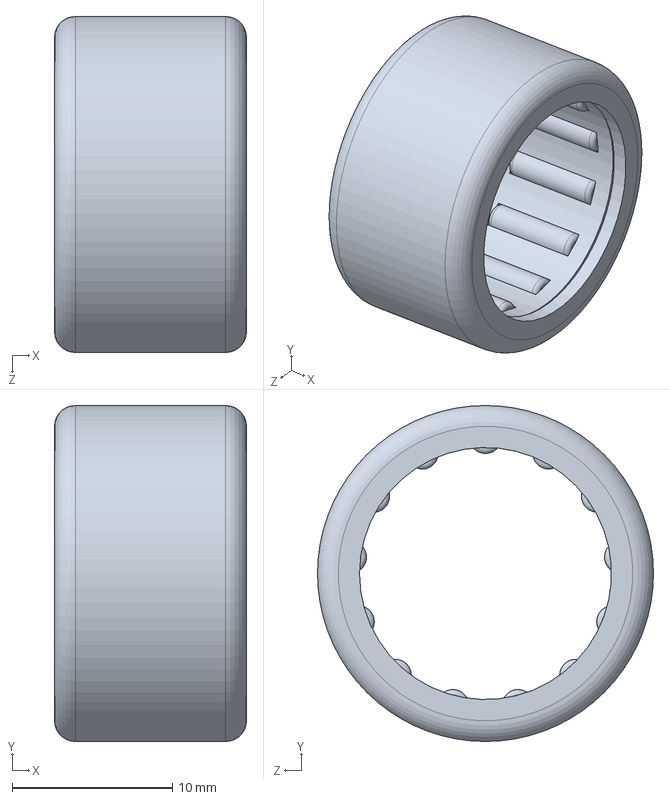
[picture p77: CAD file, 2023-01-07, last stored version]
OpenSource-Platform for publication/Ready-madeParts/HK1512.SLDPRT
12.0 x 21.0 x 21.0 mm
