yanagi-kimuralab/opensource-platform/OpenSource-Platform for publication/Parts/Circuit box_Top plate.SLDPRT

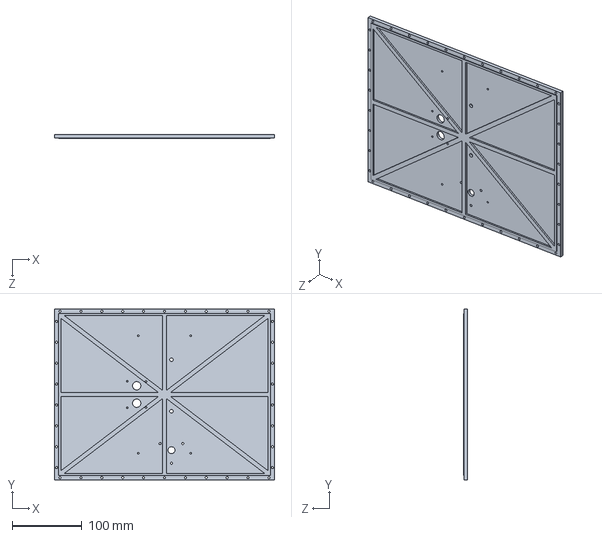
[picture p78: CAD file, 2023-01-07, last stored version]
OpenSource-Platform for publication/Parts/Circuit box_Top plate.SLDPRT
316.0 x 244.9 x 6.00 mm
