yanagi-kimuralab/opensource-platform/OpenSource-Platform for publication/Ready-madeParts/RDOS8-65-WMC4.SLDPRT

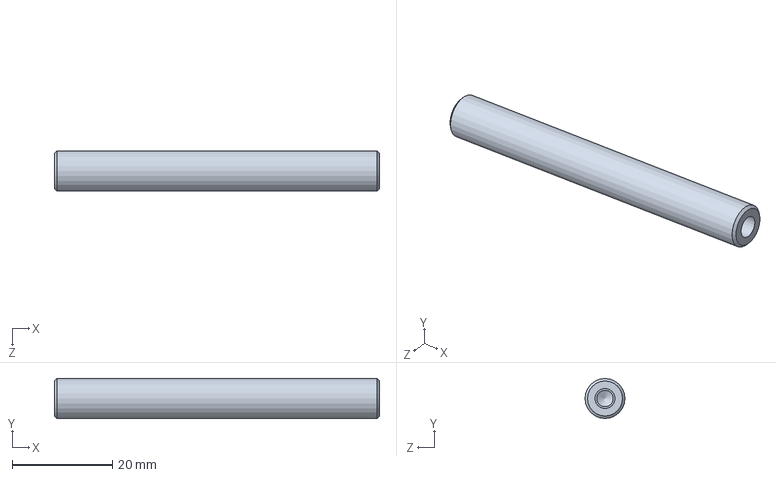
[picture p79: CAD file, 2023-01-07, last stored version]
OpenSource-Platform for publication/Ready-madeParts/RDOS8-65-WMC4.SLDPRT
65.0 x 8.00 x 8.00 mm
