yanagi-kimuralab/opensource-platform/OpenSource-Platform for publication/Ready-madeParts/maxon RE40+GP42C+HEDL5540_374679.SLDPRT

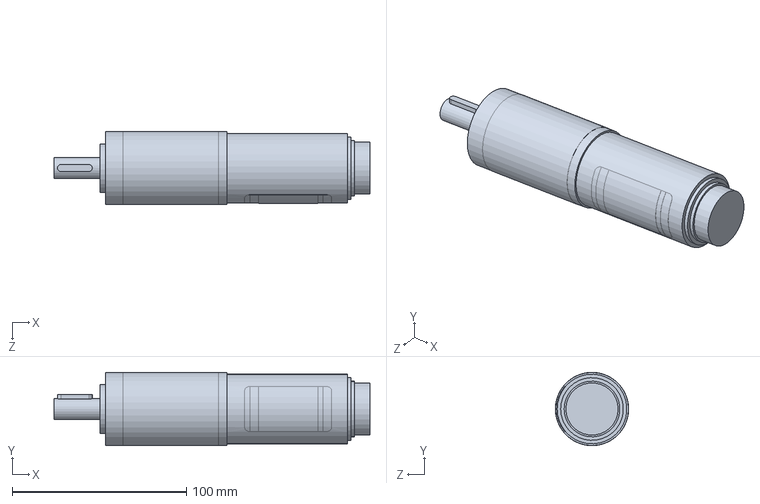
[picture p80: CAD file, 2023-01-07, last stored version]
OpenSource-Platform for publication/Ready-madeParts/maxon RE40+GP42C+HEDL5540_374679.SLDPRT
181.5 x 42.2 x 42.2 mm
