yanagi-kimuralab/opensource-platform/OpenSource-Platform for publication/Parts/Flipper_Timing pulley.SLDPRT

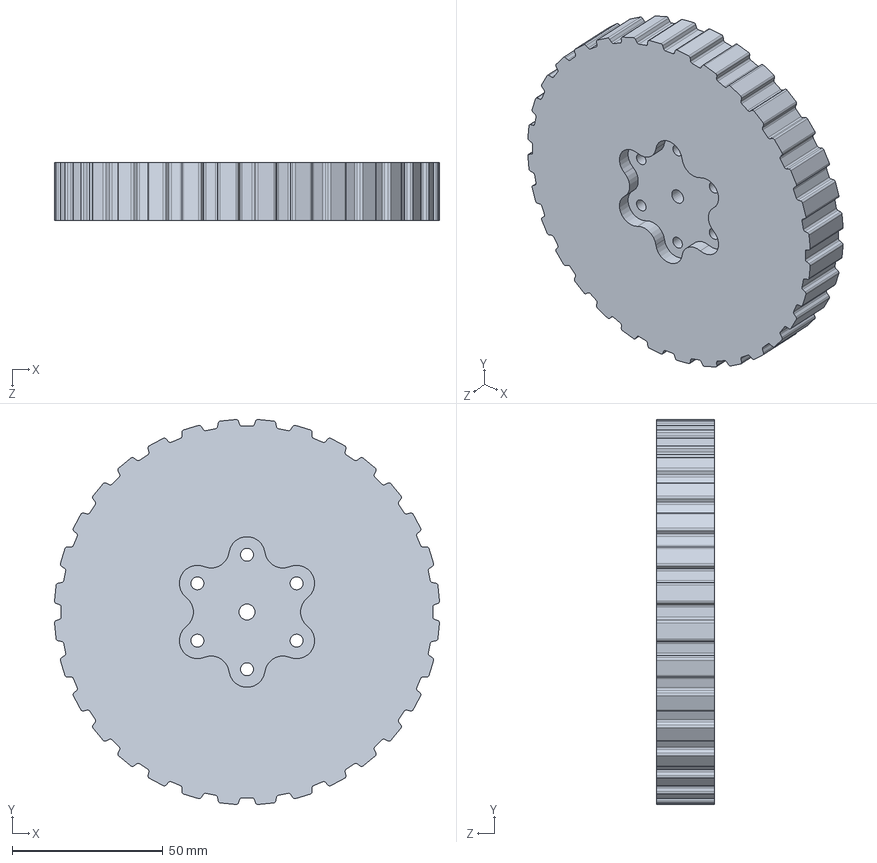
[picture p81: CAD file, 2023-01-07, last stored version]
OpenSource-Platform for publication/Parts/Flipper_Timing pulley.SLDPRT
127.8 x 127.8 x 19.1 mm
