yanagi-kimuralab/opensource-platform/OpenSource-Platform for publication/Parts/Flipper_Frame.SLDPRT

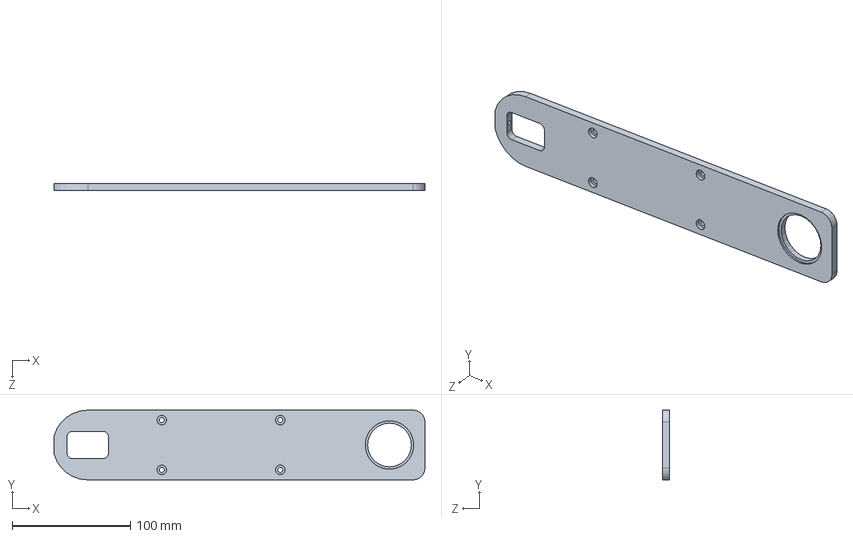
[picture p82: CAD file, 2023-01-07, last stored version]
OpenSource-Platform for publication/Parts/Flipper_Frame.SLDPRT
313.5 x 59.0 x 6.00 mm
