yanagi-kimuralab/opensource-platform/OpenSource-Platform for publication/Ready-madeParts/PG-4 NG-79-F.SLDPRT

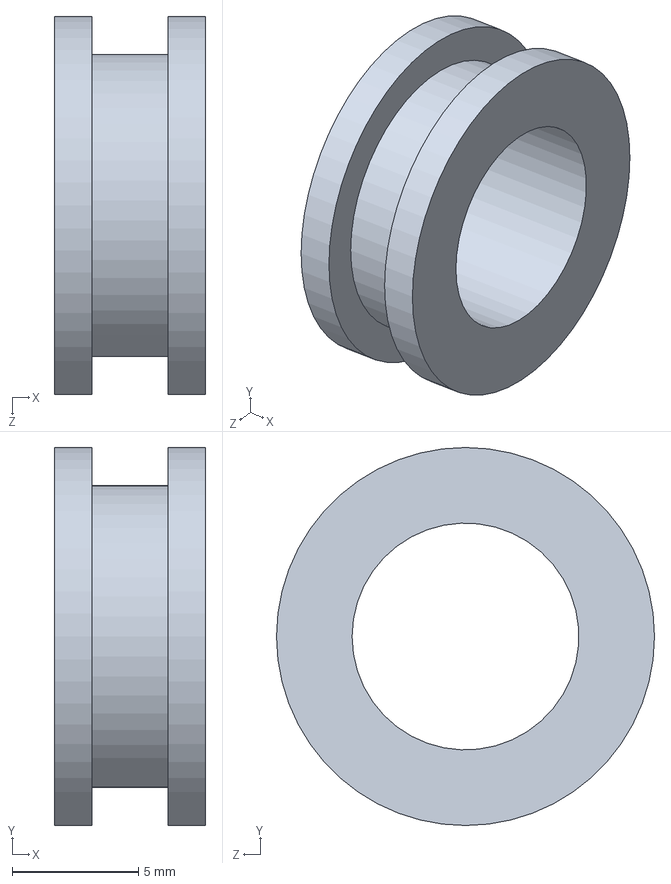
[picture p83: CAD file, 2023-01-07, last stored version]
OpenSource-Platform for publication/Ready-madeParts/PG-4 NG-79-F.SLDPRT
6.00 x 15.0 x 15.0 mm
