yanagi-kimuralab/opensource-platform/OpenSource-Platform for publication/Parts/Driving flipper_Plate covering O-ring.SLDPRT

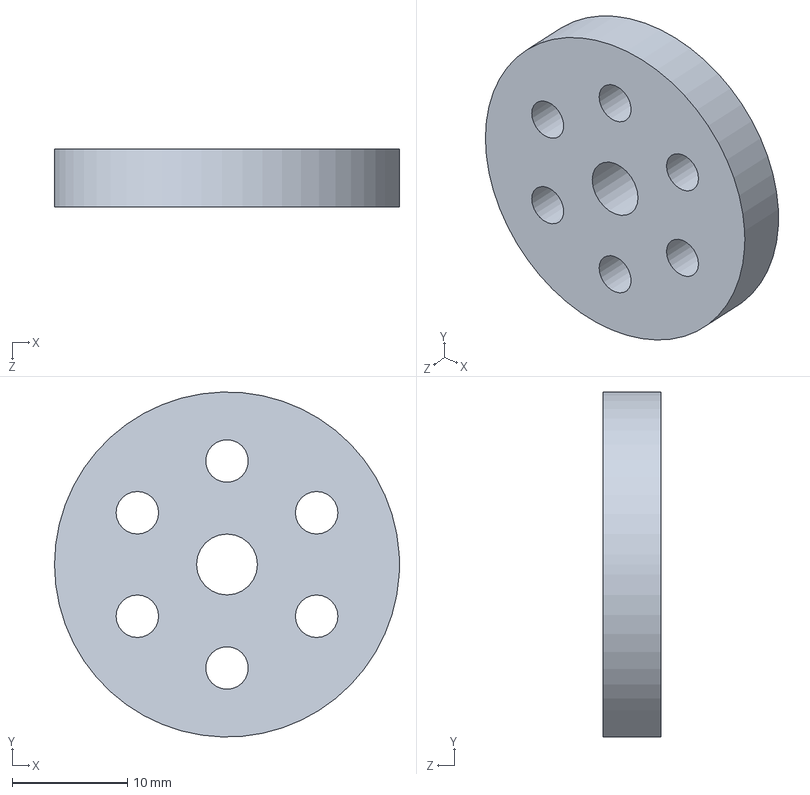
[picture p84: CAD file, 2023-01-07, last stored version]
OpenSource-Platform for publication/Parts/Driving flipper_Plate covering O-ring.SLDPRT
30.0 x 30.0 x 5.00 mm
