yanagi-kimuralab/opensource-platform/OpenSource-Platform for publication/Parts/Driving crawler_Sliding Idler.SLDPRT

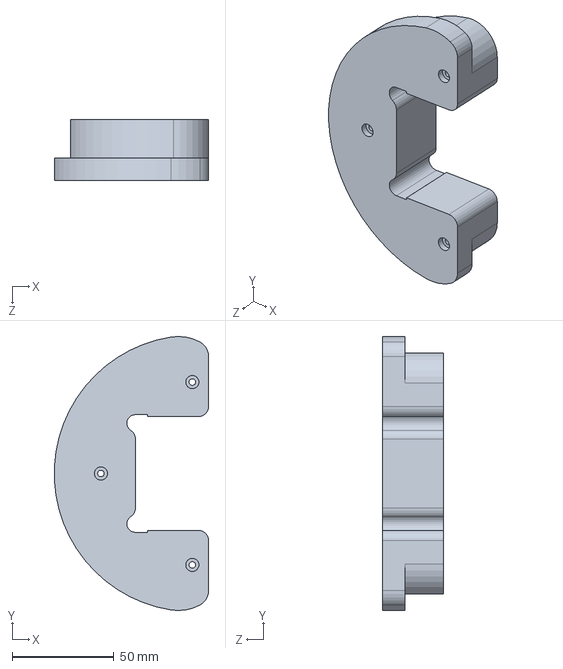
[picture p85: CAD file, 2023-01-07, last stored version]
OpenSource-Platform for publication/Parts/Driving crawler_Sliding Idler.SLDPRT
75.9 x 134.9 x 30.0 mm
