yanagi-kimuralab/opensource-platform/OpenSource-Platform for publication/Ready-madeParts/SBOX IDEC NGC-132.SLDPRT

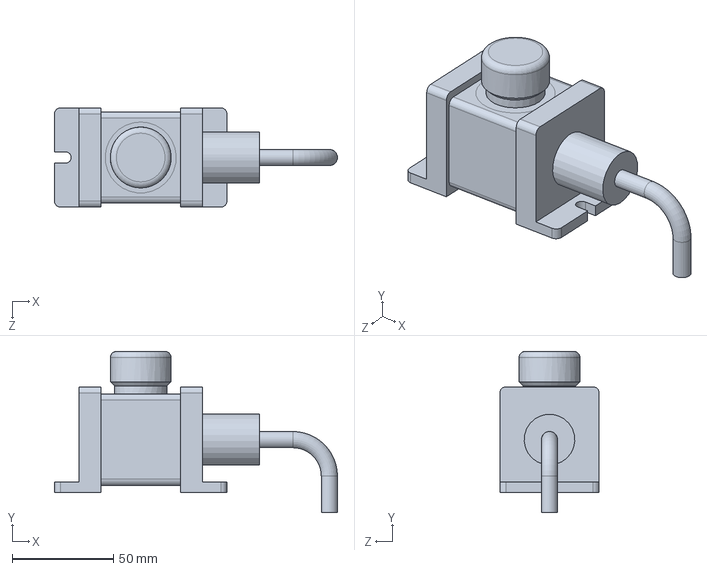
[picture p86: CAD file, 2023-01-07, last stored version]
OpenSource-Platform for publication/Ready-madeParts/SBOX IDEC NGC-132.SLDPRT
139.5 x 79.5 x 49.0 mm
