yanagi-kimuralab/opensource-platform/OpenSource-Platform for publication/Parts/Flipper_Tensioner_Positioning plate _Inside.SLDPRT

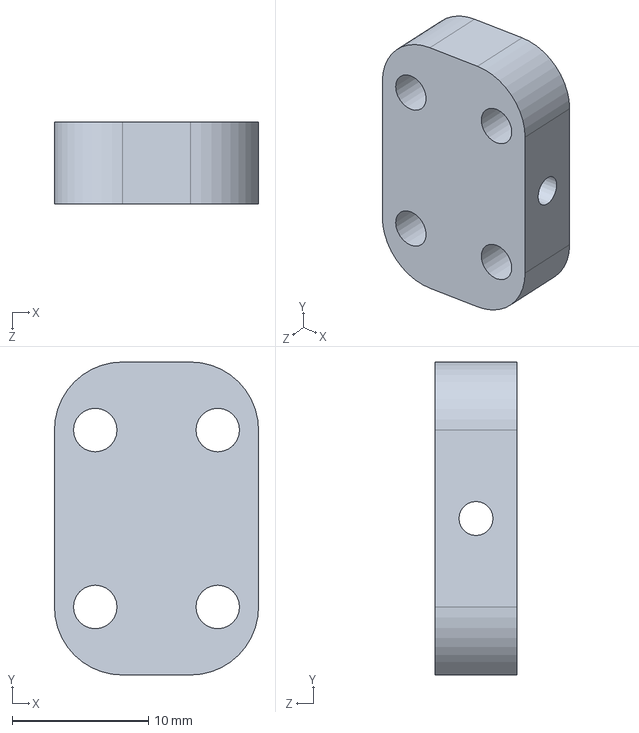
[picture p87: CAD file, 2023-01-07, last stored version]
OpenSource-Platform for publication/Parts/Flipper_Tensioner_Positioning plate _Inside.SLDPRT
15.0 x 23.0 x 6.00 mm
