yanagi-kimuralab/opensource-platform/OpenSource-Platform for publication/Ready-madeParts/RDOS8-49-WMC4.SLDPRT

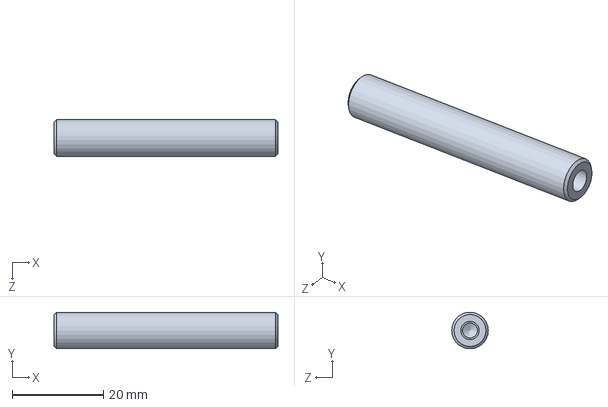
[picture p88: CAD file, 2023-01-07, last stored version]
OpenSource-Platform for publication/Ready-madeParts/RDOS8-49-WMC4.SLDPRT
49.0 x 7.94 x 8.00 mm
