yanagi-kimuralab/opensource-platform/OpenSource-Platform for publication/Parts/Driving crawler_Timing pulley_Partition plate.SLDPRT

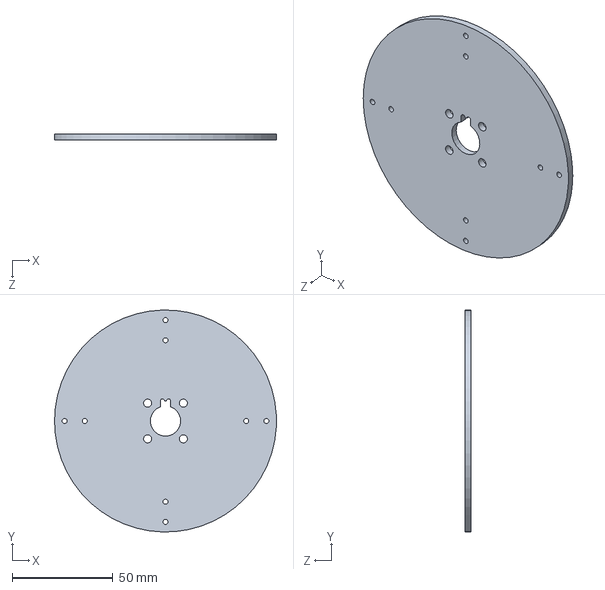
[picture p89: CAD file, 2023-01-07, last stored version]
OpenSource-Platform for publication/Parts/Driving crawler_Timing pulley_Partition plate.SLDPRT
110.0 x 110.0 x 3.00 mm
