yanagi-kimuralab/opensource-platform/OpenSource-Platform for publication/Ready-madeParts/AETRF6-20.SLDPRT

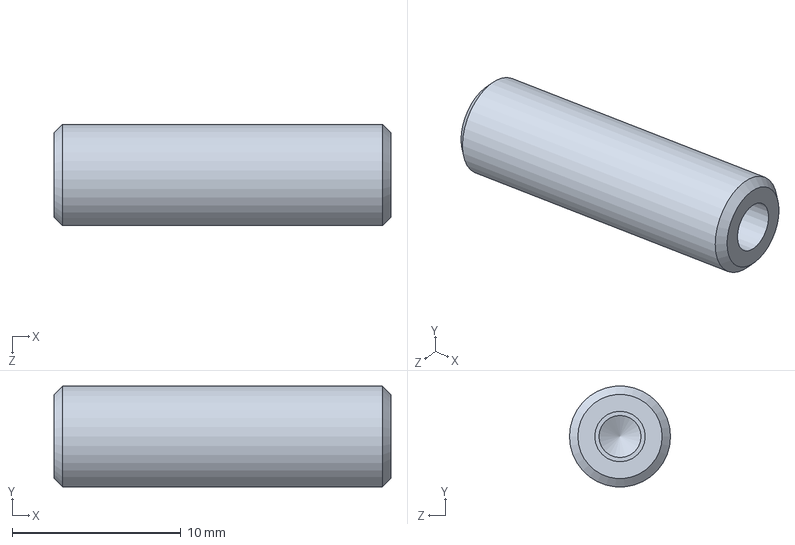
[picture p90: CAD file, 2023-01-07, last stored version]
OpenSource-Platform for publication/Ready-madeParts/AETRF6-20.SLDPRT
20.0 x 5.97 x 6.00 mm
