yanagi-kimuralab/opensource-platform/OpenSource-Platform for publication/Parts/Timing belt protection.SLDPRT

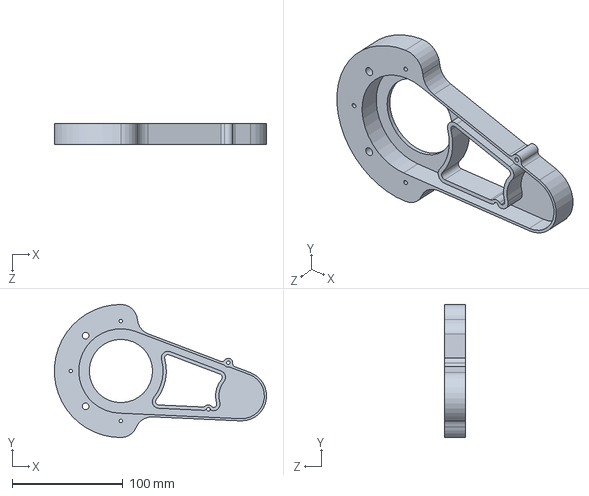
[picture p91: CAD file, 2023-01-07, last stored version]
OpenSource-Platform for publication/Parts/Timing belt protection.SLDPRT
191.1 x 120.0 x 18.8 mm
