yanagi-kimuralab/opensource-platform/OpenSource-Platform for publication/Ready-madeParts/KRT AWG28 X 8C 3m.sldprt

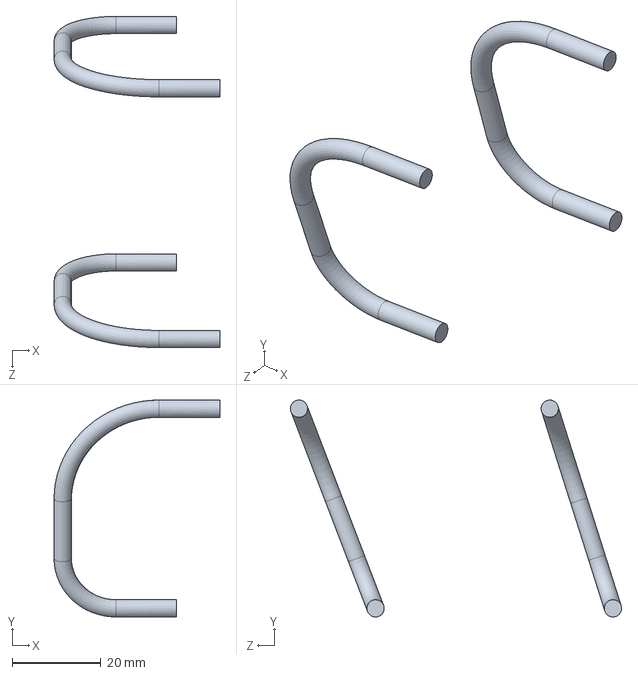
[picture p92: CAD file, 2023-01-07, last stored version]
OpenSource-Platform for publication/Ready-madeParts/KRT AWG28 X 8C 3m.sldprt
37.4 x 48.9 x 74.7 mm
