yanagi-kimuralab/opensource-platform/OpenSource-Platform for publication/Parts/Flipper_Tensioner_Positioning plate _Outside.SLDPRT

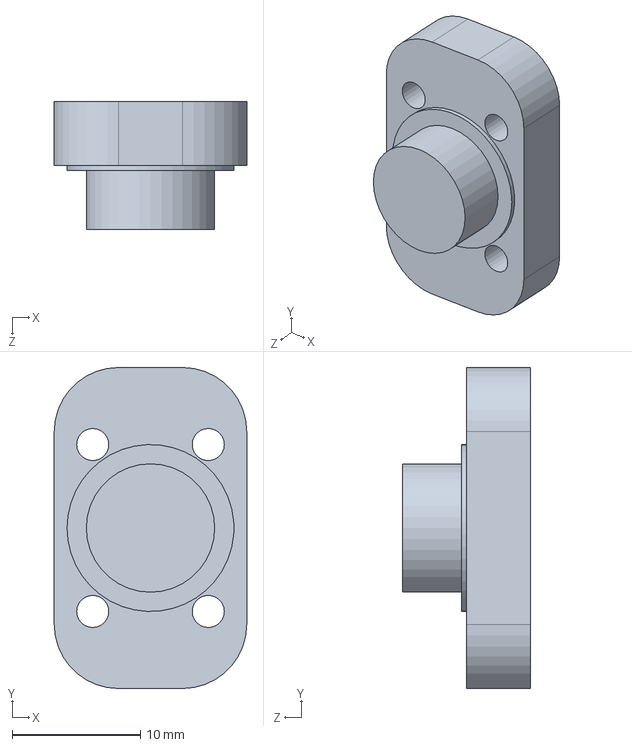
[picture p93: CAD file, 2023-01-07, last stored version]
OpenSource-Platform for publication/Parts/Flipper_Tensioner_Positioning plate _Outside.SLDPRT
15.0 x 25.0 x 10.0 mm
