yanagi-kimuralab/opensource-platform/OpenSource-Platform for publication/Ready-madeParts/MTS5M390G.SLDPRT

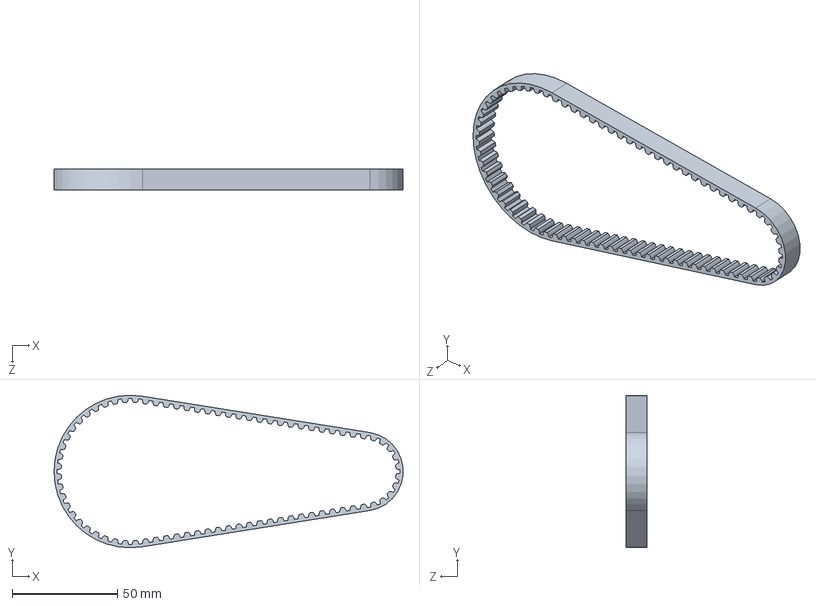
[picture p94: CAD file, 2023-01-07, last stored version]
OpenSource-Platform for publication/Ready-madeParts/MTS5M390G.SLDPRT
166.0 x 72.5 x 10.0 mm
