yanagi-kimuralab/opensource-platform/OpenSource-Platform for publication/Parts/Circuit box_Bottom plate.SLDPRT

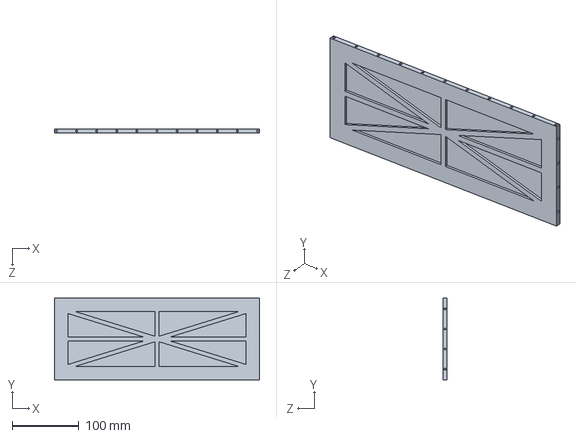
[picture p95: CAD file, 2023-01-07, last stored version]
OpenSource-Platform for publication/Parts/Circuit box_Bottom plate.SLDPRT
306.0 x 122.4 x 6.00 mm
