yanagi-kimuralab/opensource-platform/OpenSource-Platform for publication/Ready-madeParts/Rubber sheet with CR cloth.sldprt

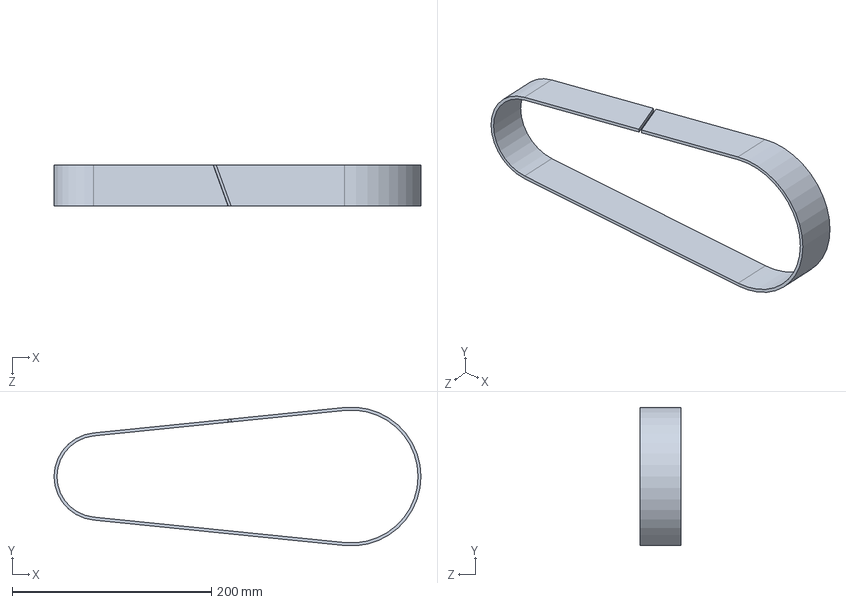
[picture p96: CAD file, 2023-01-07, last stored version]
OpenSource-Platform for publication/Ready-madeParts/Rubber sheet with CR cloth.sldprt
368.7 x 139.1 x 41.1 mm
