yanagi-kimuralab/opensource-platform/OpenSource-Platform for publication/Parts/Driving crawler_Timing pulley_Center attachment_Near motor.SLDPRT

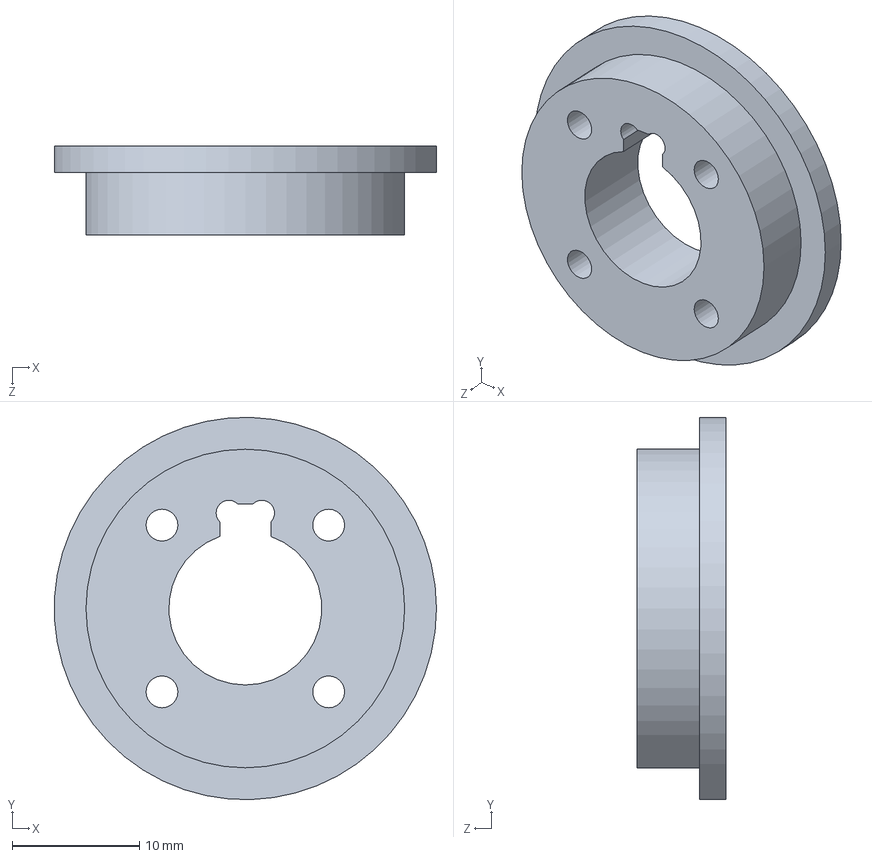
[picture p97: CAD file, 2023-01-07, last stored version]
OpenSource-Platform for publication/Parts/Driving crawler_Timing pulley_Center attachment_Near motor.SLDPRT
30.0 x 30.0 x 7.00 mm
