yanagi-kimuralab/opensource-platform/OpenSource-Platform for publication/Ready-madeParts/CPL-100(60).SLDPRT

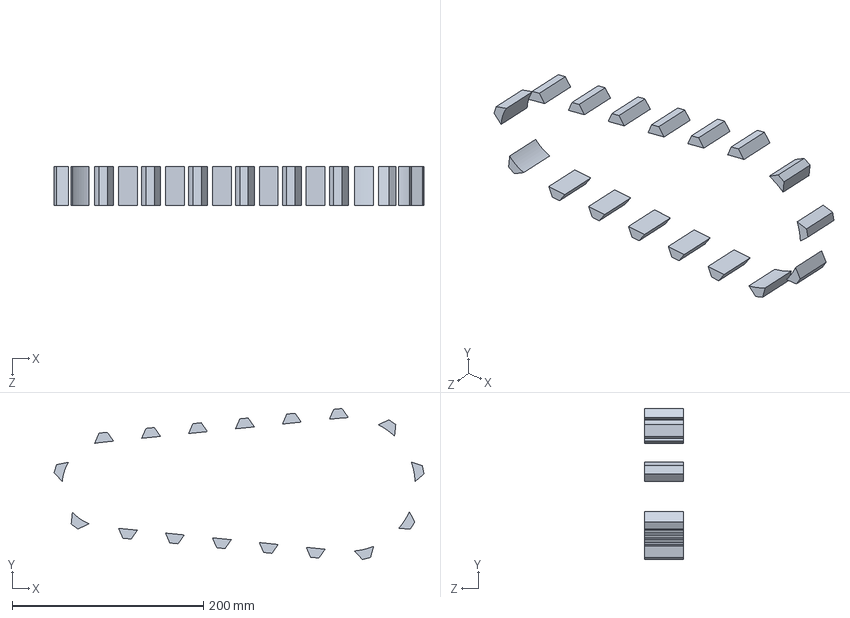
[picture p98: CAD file, 2023-01-07, last stored version]
OpenSource-Platform for publication/Ready-madeParts/CPL-100(60).SLDPRT
386.8 x 157.9 x 41.1 mm
