yanagi-kimuralab/opensource-platform/OpenSource-Platform for publication/Parts/Emergency stop switch grommet mount.SLDPRT

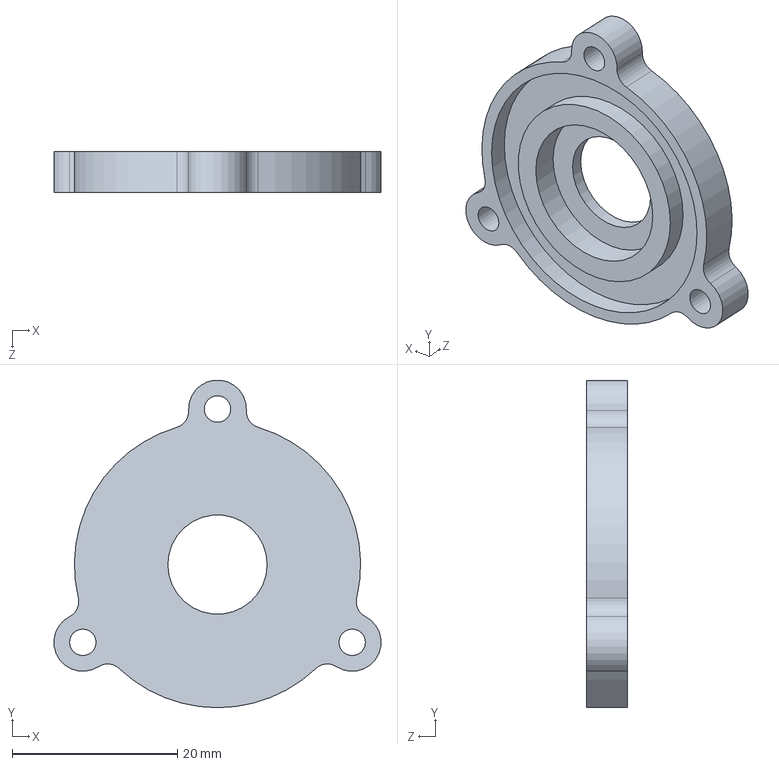
[picture p99: CAD file, 2023-01-07, last stored version]
OpenSource-Platform for publication/Parts/Emergency stop switch grommet mount.SLDPRT
39.5 x 39.6 x 5.00 mm
