yanagi-kimuralab/opensource-platform/OpenSource-Platform for publication/Ready-madeParts/6806DDU(ZZ).SLDPRT

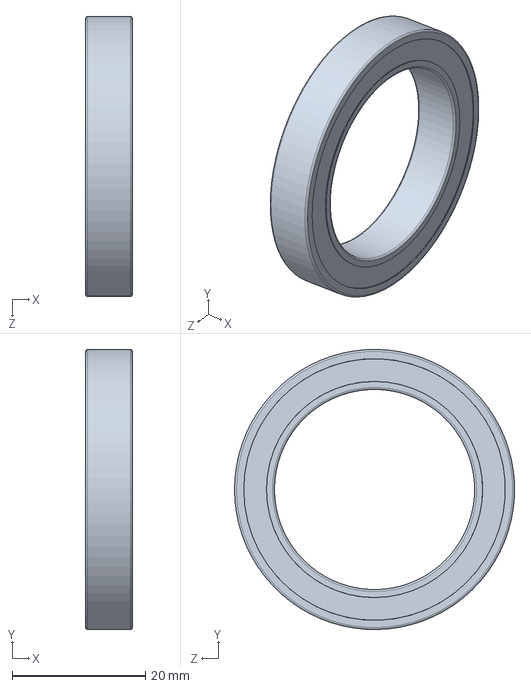
[picture p100: CAD file, 2023-01-07, last stored version]
OpenSource-Platform for publication/Ready-madeParts/6806DDU(ZZ).SLDPRT
7.00 x 42.0 x 42.0 mm
