yanagi-kimuralab/opensource-platform/OpenSource-Platform for publication/Parts/Driving crawler_Timing pulley_Center attachment.SLDPRT

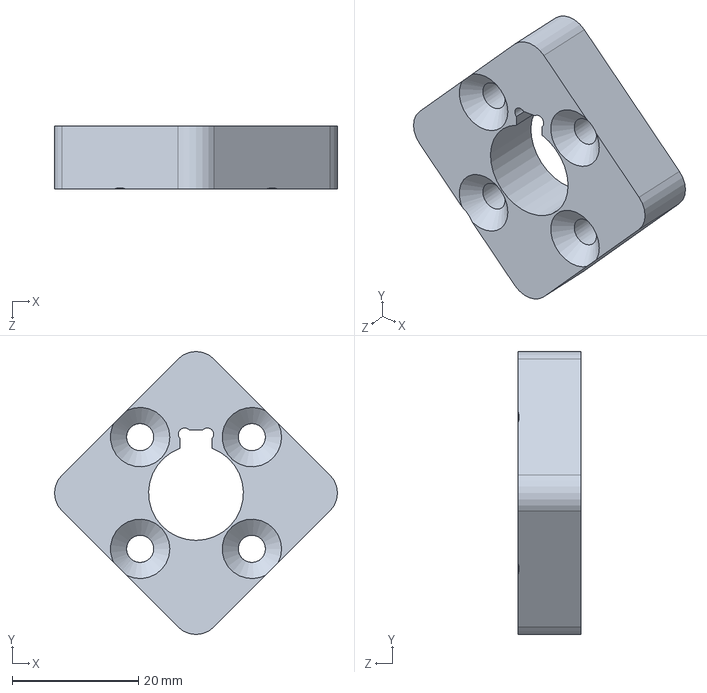
[picture p101: CAD file, 2023-01-07, last stored version]
OpenSource-Platform for publication/Parts/Driving crawler_Timing pulley_Center attachment.SLDPRT
44.8 x 44.8 x 10.0 mm
