yanagi-kimuralab/opensource-platform/OpenSource-Platform for publication/Ready-madeParts/6802DDU(ZZ).SLDPRT

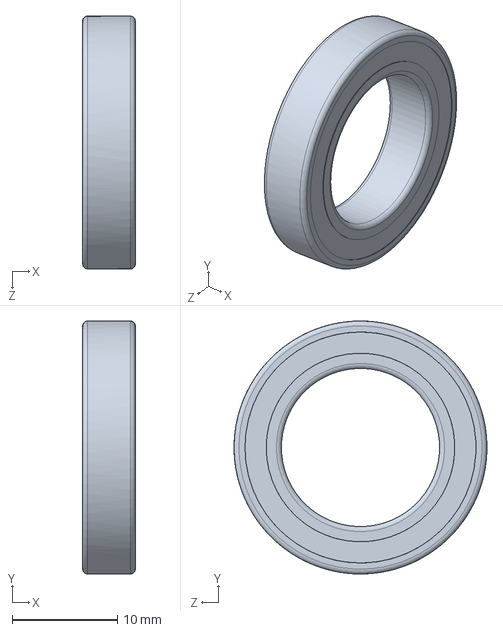
[picture p102: CAD file, 2023-01-07, last stored version]
OpenSource-Platform for publication/Ready-madeParts/6802DDU(ZZ).SLDPRT
5.00 x 24.0 x 24.0 mm
