yanagi-kimuralab/opensource-platform/OpenSource-Platform for publication/Parts/Rear part.sldprt

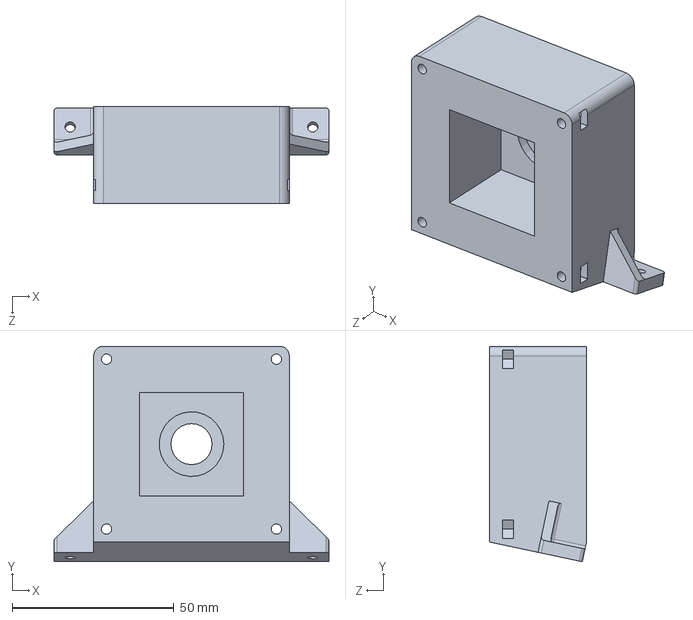
[picture p103: CAD file, 2023-01-07, last stored version]
OpenSource-Platform for publication/Parts/Rear part.sldprt
85.0 x 66.6 x 30.0 mm
