yanagi-kimuralab/opensource-platform/OpenSource-Platform for publication/Ready-madeParts/PIJJ14-8-58.SLDPRT

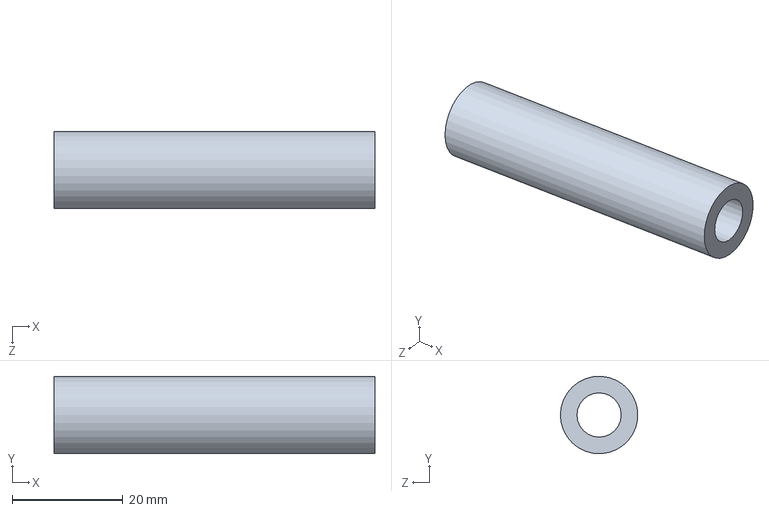
[picture p104: CAD file, 2023-01-07, last stored version]
OpenSource-Platform for publication/Ready-madeParts/PIJJ14-8-58.SLDPRT
58.0 x 14.0 x 14.0 mm
