yanagi-kimuralab/opensource-platform/OpenSource-Platform for publication/Ready-madeParts/PG-6 SG-12A.SLDPRT

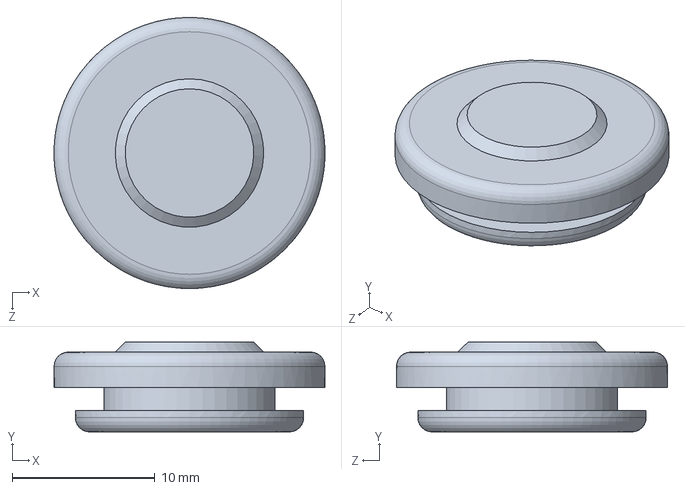
[picture p106: CAD file, 2023-01-07, last stored version]
OpenSource-Platform for publication/Ready-madeParts/PG-6 SG-12A.SLDPRT
19.0 x 6.30 x 19.0 mm
