yanagi-kimuralab/opensource-platform/OpenSource-Platform for publication/Parts/Flipper_Crawler belt.SLDPRT

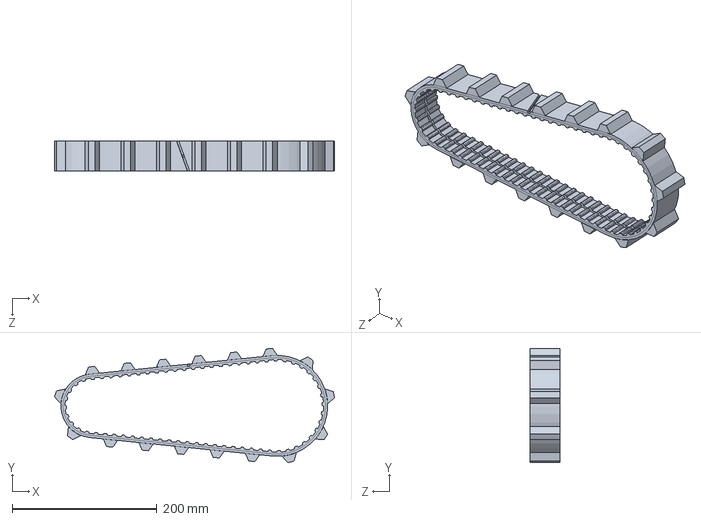
[picture p107: CAD file, 2023-01-07, last stored version]
OpenSource-Platform for publication/Parts/Flipper_Crawler belt.SLDPRT
386.8 x 157.9 x 41.1 mm
