yanagi-kimuralab/opensource-platform/OpenSource-Platform for publication/Ready-madeParts/KZES15-106-T10-P15-LA42-NA5-KB18-HB23-AA180-WA0-GA16.SLDPRT

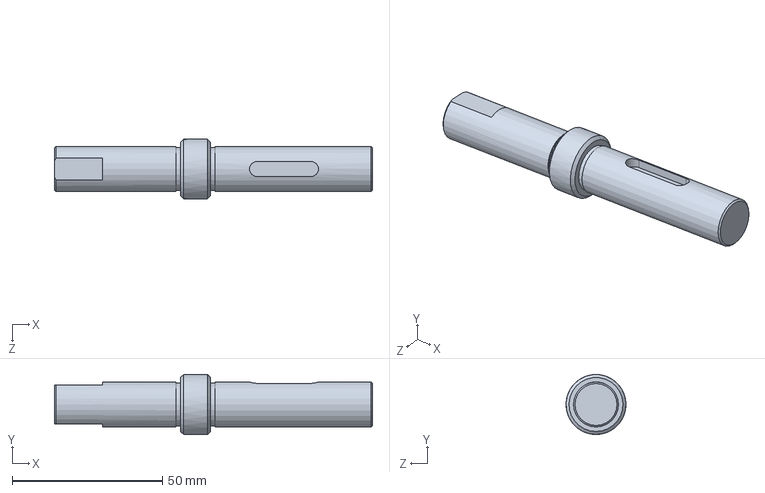
[picture p108: CAD file, 2023-01-07, last stored version]
OpenSource-Platform for publication/Ready-madeParts/KZES15-106-T10-P15-LA42-NA5-KB18-HB23-AA180-WA0-GA16.SLDPRT
106.0 x 20.0 x 20.0 mm
