yanagi-kimuralab/opensource-platform/OpenSource-Platform for publication/Parts/Flipper_Idler.SLDPRT

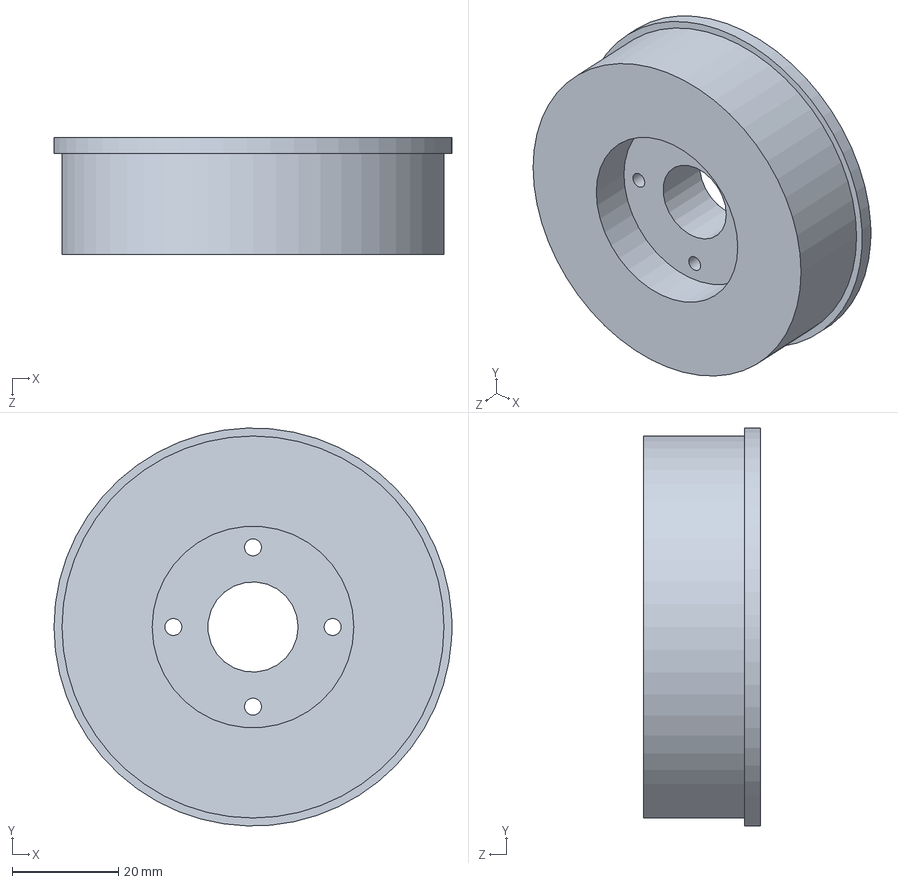
[picture p109: CAD file, 2023-01-07, last stored version]
OpenSource-Platform for publication/Parts/Flipper_Idler.SLDPRT
75.0 x 75.0 x 22.1 mm
