yanagi-kimuralab/opensource-platform/OpenSource-Platform for publication/Ready-madeParts/PIJJ20-8-90.SLDPRT

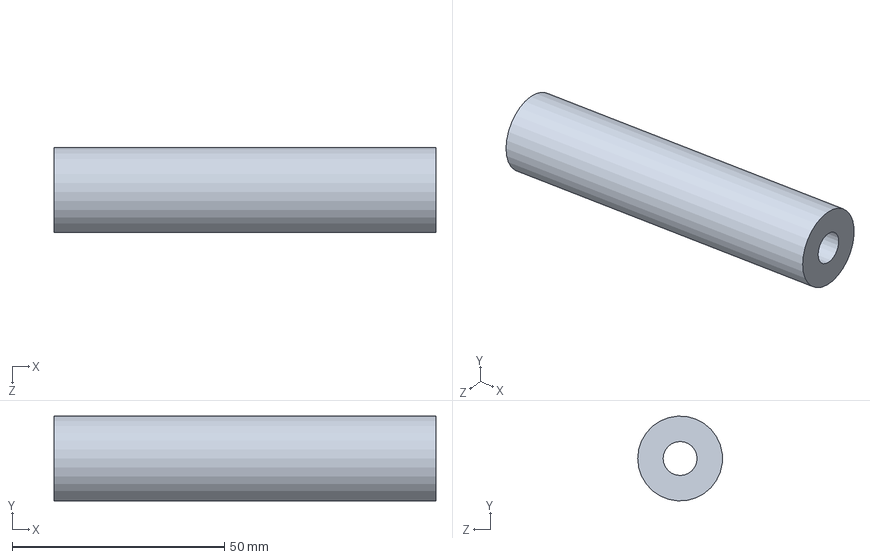
[picture p110: CAD file, 2023-01-07, last stored version]
OpenSource-Platform for publication/Ready-madeParts/PIJJ20-8-90.SLDPRT
90.0 x 20.0 x 19.9 mm
