yanagi-kimuralab/opensource-platform/OpenSource-Platform for publication/Parts/Circuit box_Under loft plate.SLDPRT

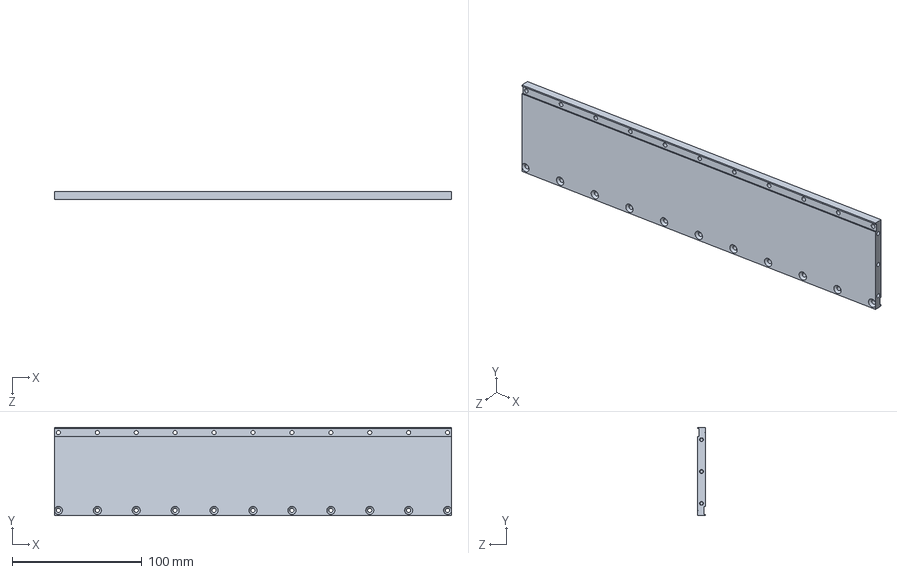
[picture p111: CAD file, 2023-01-07, last stored version]
OpenSource-Platform for publication/Parts/Circuit box_Under loft plate.SLDPRT
306.0 x 68.0 x 6.00 mm
