yanagi-kimuralab/opensource-platform/OpenSource-Platform for publication/Ready-madeParts/ORG55.SLDPRT

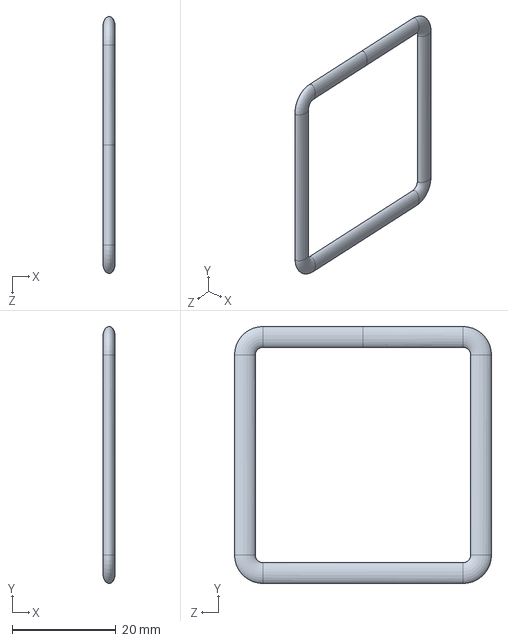
[picture p112: CAD file, 2023-01-07, last stored version]
OpenSource-Platform for publication/Ready-madeParts/ORG55.SLDPRT
2.39 x 49.5 x 49.5 mm
