yanagi-kimuralab/opensource-platform/OpenSource-Platform for publication/Parts/Circuit box_Plate_Side L R.SLDPRT

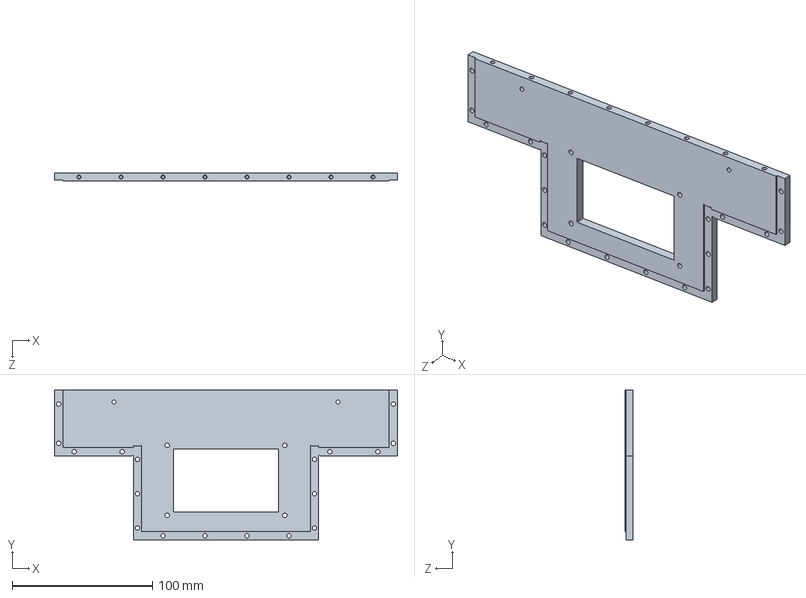
[picture p113: CAD file, 2023-01-07, last stored version]
OpenSource-Platform for publication/Parts/Circuit box_Plate_Side L R.SLDPRT
244.9 x 107.0 x 6.00 mm
