yanagi-kimuralab/opensource-platform/OpenSource-Platform for publication/Parts/Connecting rod_Top.SLDPRT

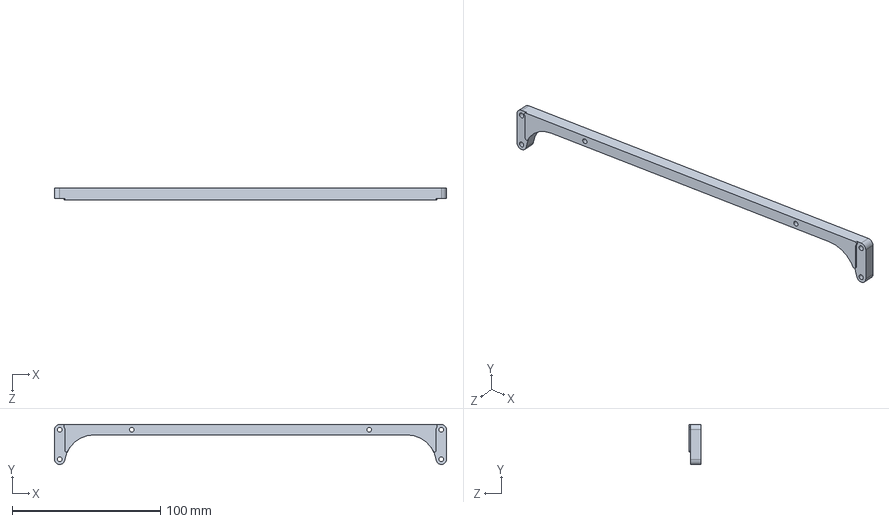
[picture p114: CAD file, 2023-01-07, last stored version]
OpenSource-Platform for publication/Parts/Connecting rod_Top.SLDPRT
264.4 x 27.0 x 8.00 mm
