yanagi-kimuralab/opensource-platform/OpenSource-Platform for publication/Parts/Flipper_Sliding guide.SLDPRT

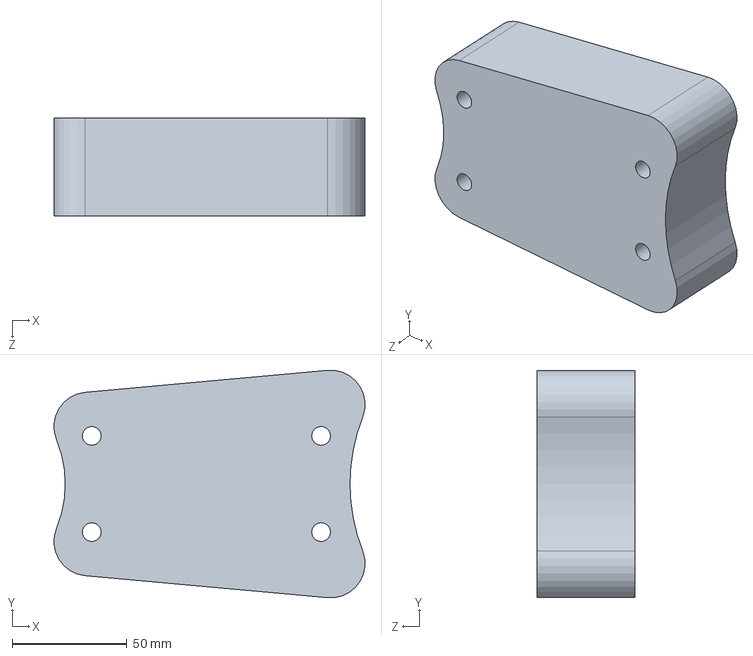
[picture p115: CAD file, 2023-01-07, last stored version]
OpenSource-Platform for publication/Parts/Flipper_Sliding guide.SLDPRT
135.8 x 99.3 x 43.0 mm
