yanagi-kimuralab/opensource-platform/OpenSource-Platform for publication/Parts/Driving flipper_Motor box_Plate_Side L R.SLDPRT

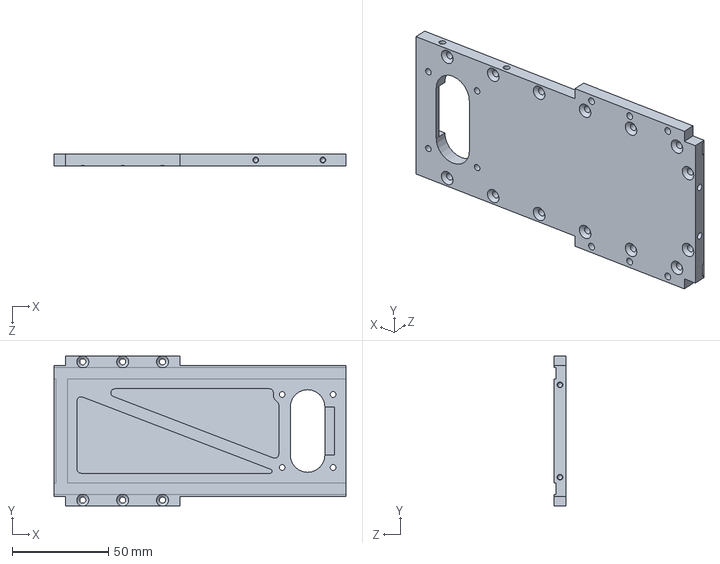
[picture p116: CAD file, 2023-01-07, last stored version]
OpenSource-Platform for publication/Parts/Driving flipper_Motor box_Plate_Side L R.SLDPRT
152.0 x 78.0 x 6.00 mm
