yanagi-kimuralab/opensource-platform/OpenSource-Platform for publication/Parts/Driving flipper_Motor box_Inside cap.SLDPRT

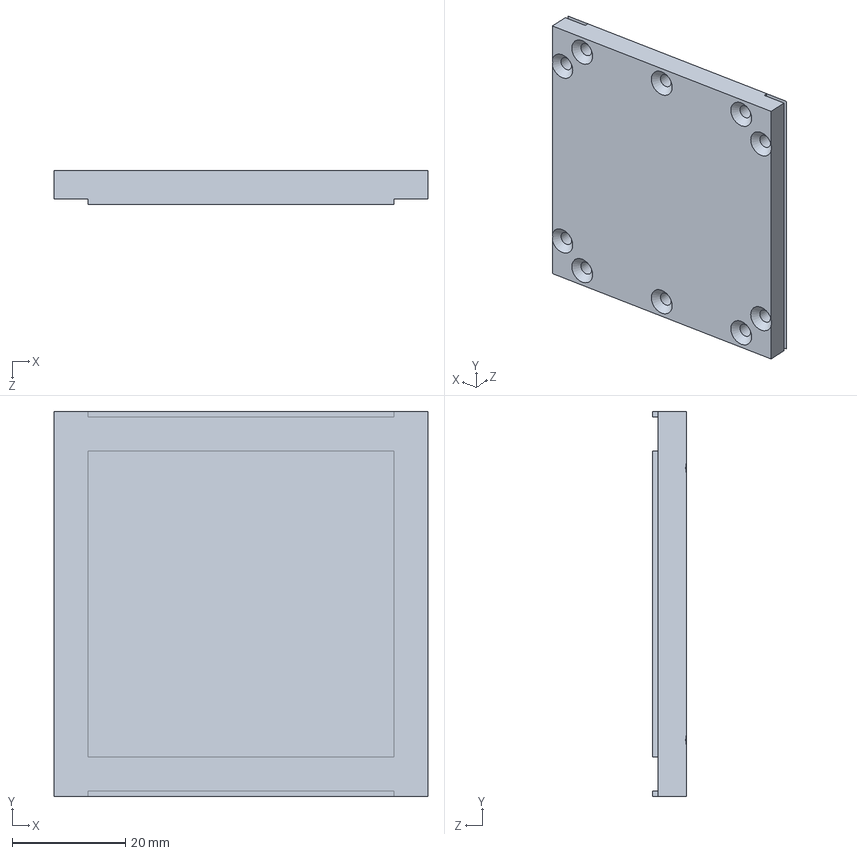
[picture p117: CAD file, 2023-01-07, last stored version]
OpenSource-Platform for publication/Parts/Driving flipper_Motor box_Inside cap.SLDPRT
66.0 x 68.0 x 6.00 mm
