yanagi-kimuralab/opensource-platform/OpenSource-Platform for publication/Parts/Connecting plate.SLDPRT

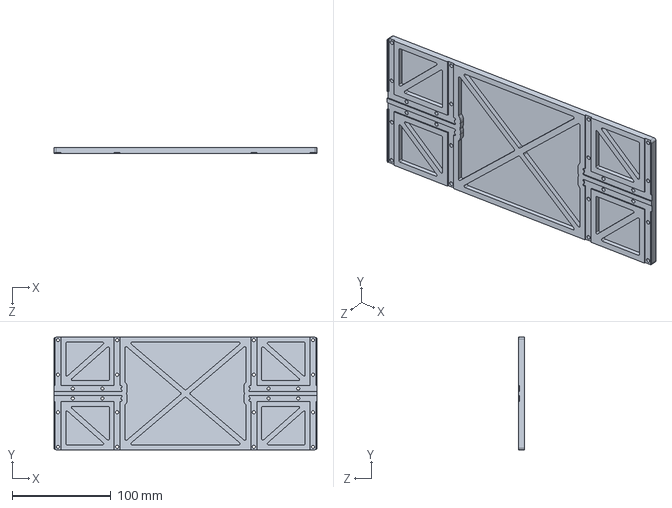
[picture p118: CAD file, 2023-01-07, last stored version]
OpenSource-Platform for publication/Parts/Connecting plate.SLDPRT
266.4 x 114.0 x 6.00 mm
