yanagi-kimuralab/opensource-platform/OpenSource-Platform for publication/Parts/Timing belt protection_Mirror.SLDPRT

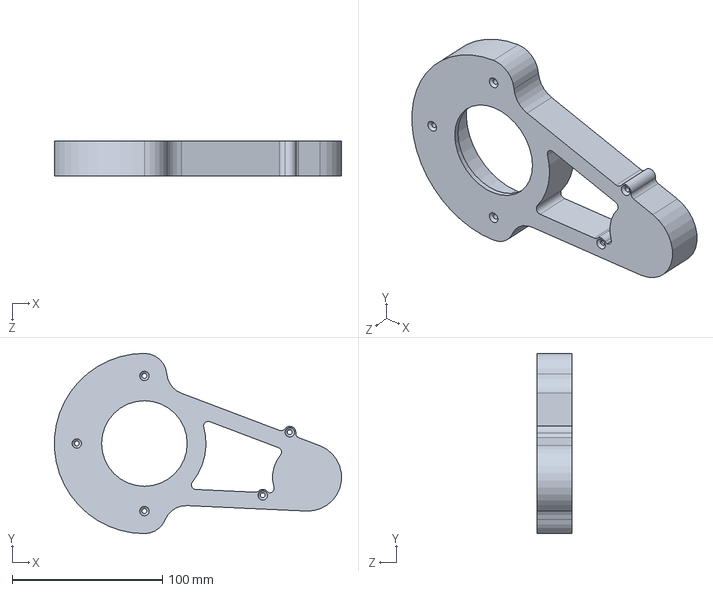
[picture p119: CAD file, 2023-01-07, last stored version]
OpenSource-Platform for publication/Parts/Timing belt protection_Mirror.SLDPRT
191.1 x 120.0 x 23.0 mm
