yanagi-kimuralab/opensource-platform/OpenSource-Platform for publication/Parts/Driving flipper_Grommet mounting plate.SLDPRT

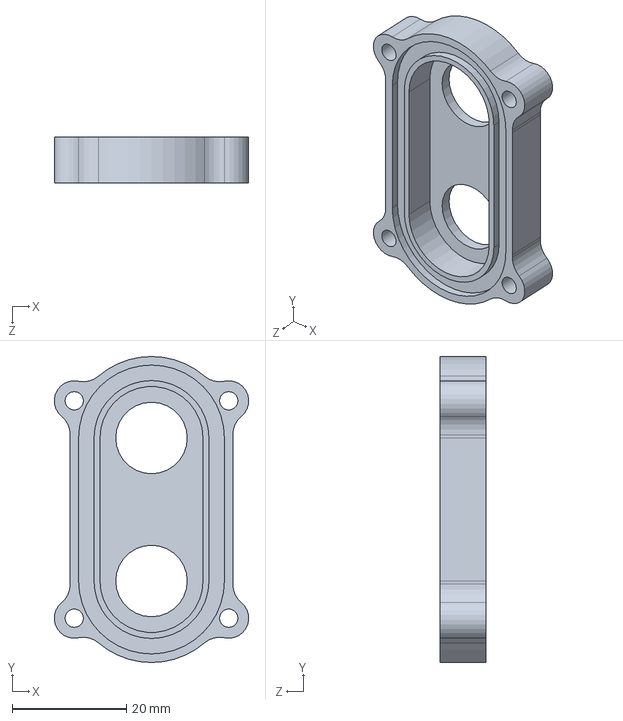
[picture p120: CAD file, 2023-01-07, last stored version]
OpenSource-Platform for publication/Parts/Driving flipper_Grommet mounting plate.SLDPRT
34.0 x 53.5 x 8.00 mm
