yanagi-kimuralab/opensource-platform/OpenSource-Platform for publication/Parts/Driving crawler_Timing pulley.SLDPRT

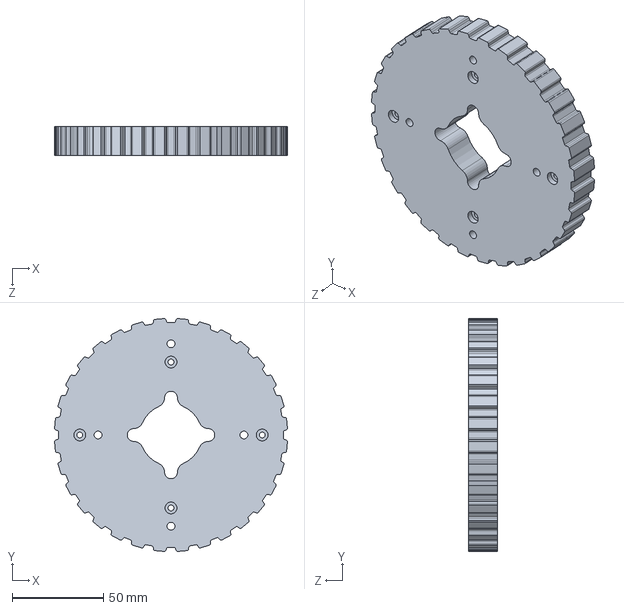
[picture p121: CAD file, 2023-01-07, last stored version]
OpenSource-Platform for publication/Parts/Driving crawler_Timing pulley.SLDPRT
127.8 x 127.8 x 16.0 mm
