yanagi-kimuralab/opensource-platform/OpenSource-Platform for publication/Parts/Circuit box_Loft plate.SLDPRT

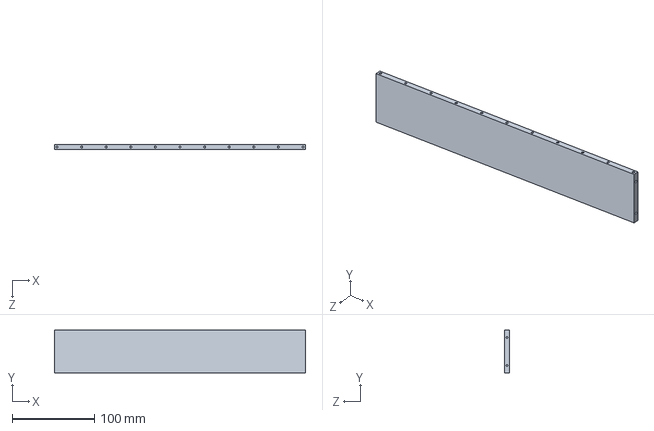
[picture p122: CAD file, 2023-01-07, last stored version]
OpenSource-Platform for publication/Parts/Circuit box_Loft plate.SLDPRT
306.0 x 52.3 x 6.00 mm
