yanagi-kimuralab/opensource-platform/OpenSource-Platform for publication/Parts/Driving crawler_Sliding Idler Outside .SLDPRT

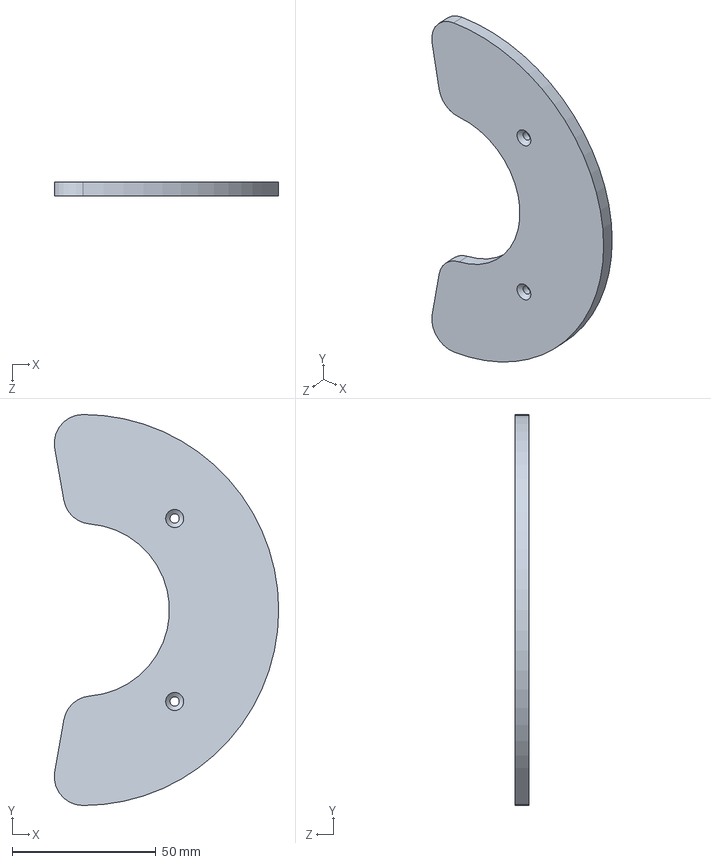
[picture p123: CAD file, 2023-01-07, last stored version]
OpenSource-Platform for publication/Parts/Driving crawler_Sliding Idler Outside .SLDPRT
78.0 x 136.0 x 5.00 mm
