yanagi-kimuralab/opensource-platform/OpenSource-Platform for publication/Parts/Lower roller_Connecting rod_Bottom.SLDPRT

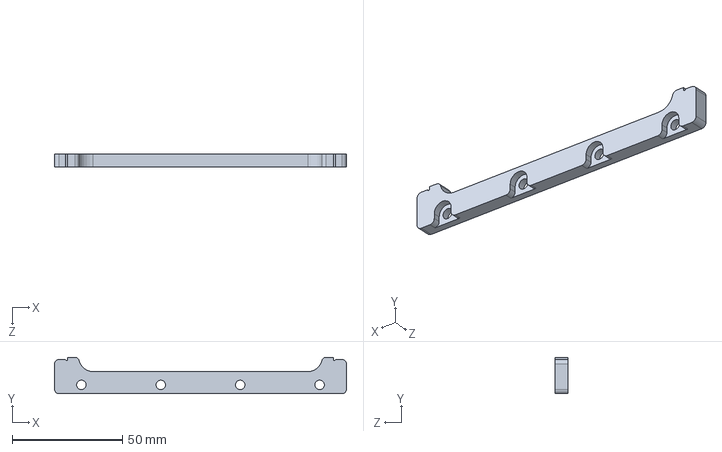
[picture p124: CAD file, 2023-01-07, last stored version]
OpenSource-Platform for publication/Parts/Lower roller_Connecting rod_Bottom.SLDPRT
132.4 x 16.5 x 6.00 mm
